bvbvbv54/ELKATEB-Hydrolic-Handbrake/prototype_commercial_v1/renders/01_FRONT_LEFT_3Q.png

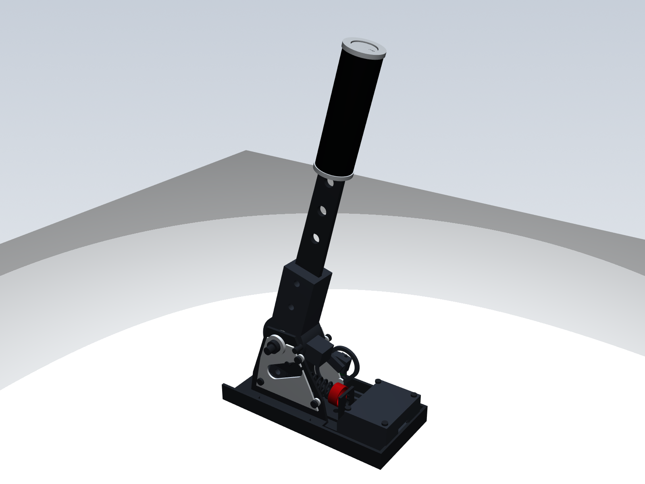
prototype_commercial_v1/renders/01_FRONT_LEFT_3Q.png
