bvbvbv54/ELKATEB-Hydrolic-Handbrake/prototype_commercial_v1/renders/02_FRONT_RIGHT_3Q.png

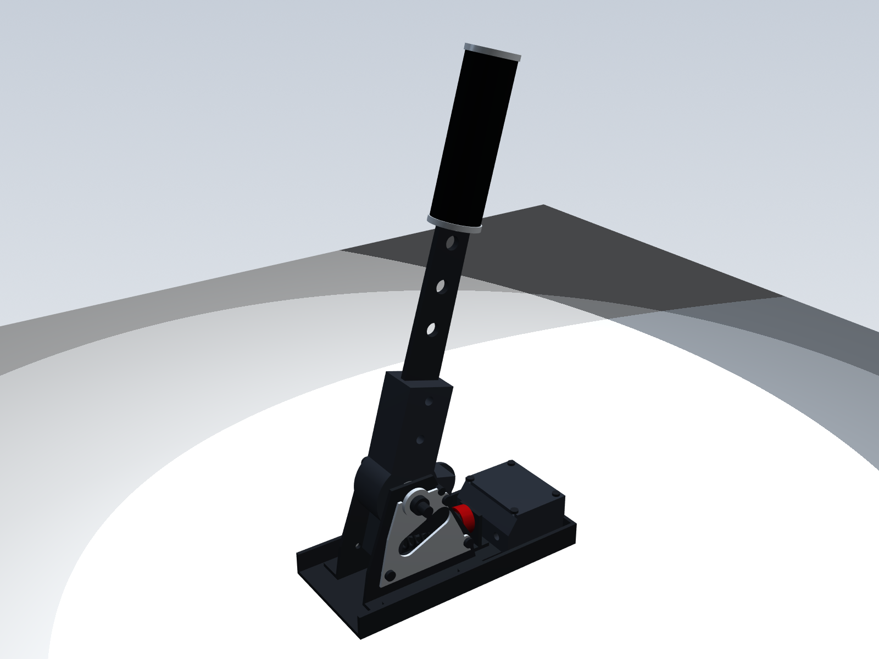
prototype_commercial_v1/renders/02_FRONT_RIGHT_3Q.png
