bvbvbv54/ELKATEB-Hydrolic-Handbrake/prototype_commercial_v1/renders/03_LEFT_SIDE.png

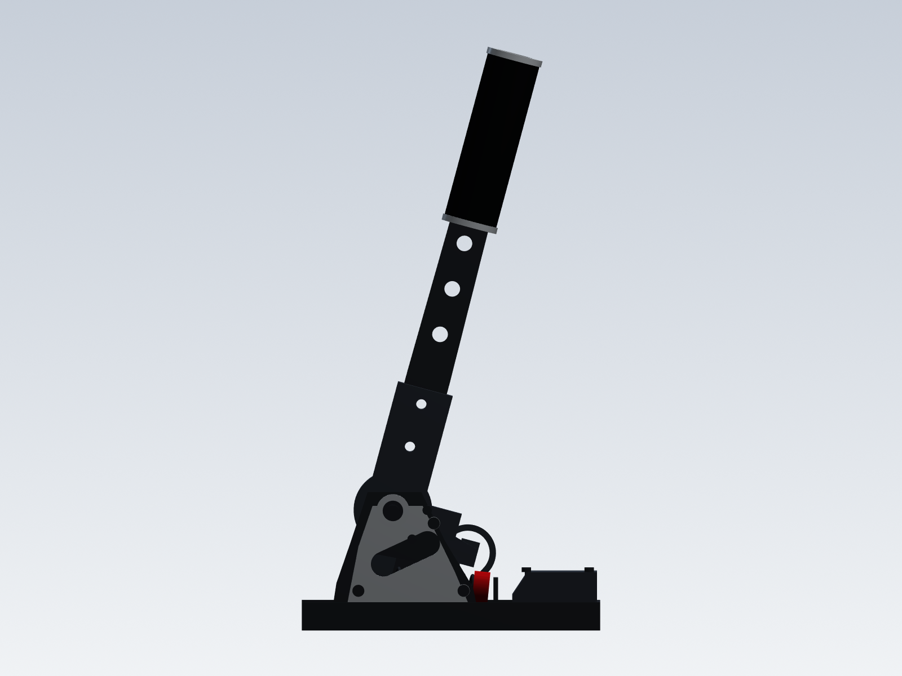
prototype_commercial_v1/renders/03_LEFT_SIDE.png
