bvbvbv54/ELKATEB-Hydrolic-Handbrake/prototype_commercial_v1/renders/07_TOP.png

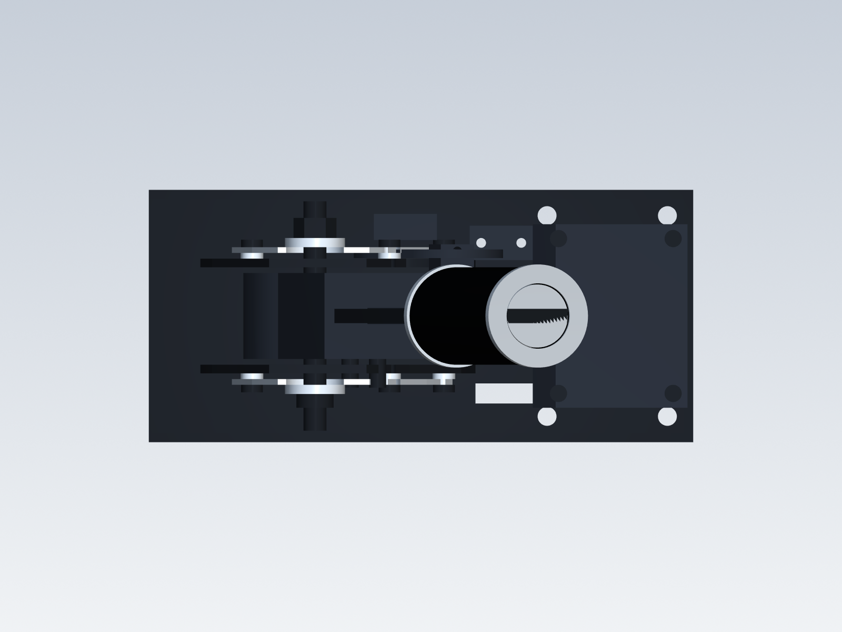
prototype_commercial_v1/renders/07_TOP.png
