bvbvbv54/ELKATEB-Hydrolic-Handbrake/prototype_commercial_v1/renders/08_LOW_ANGLE.png

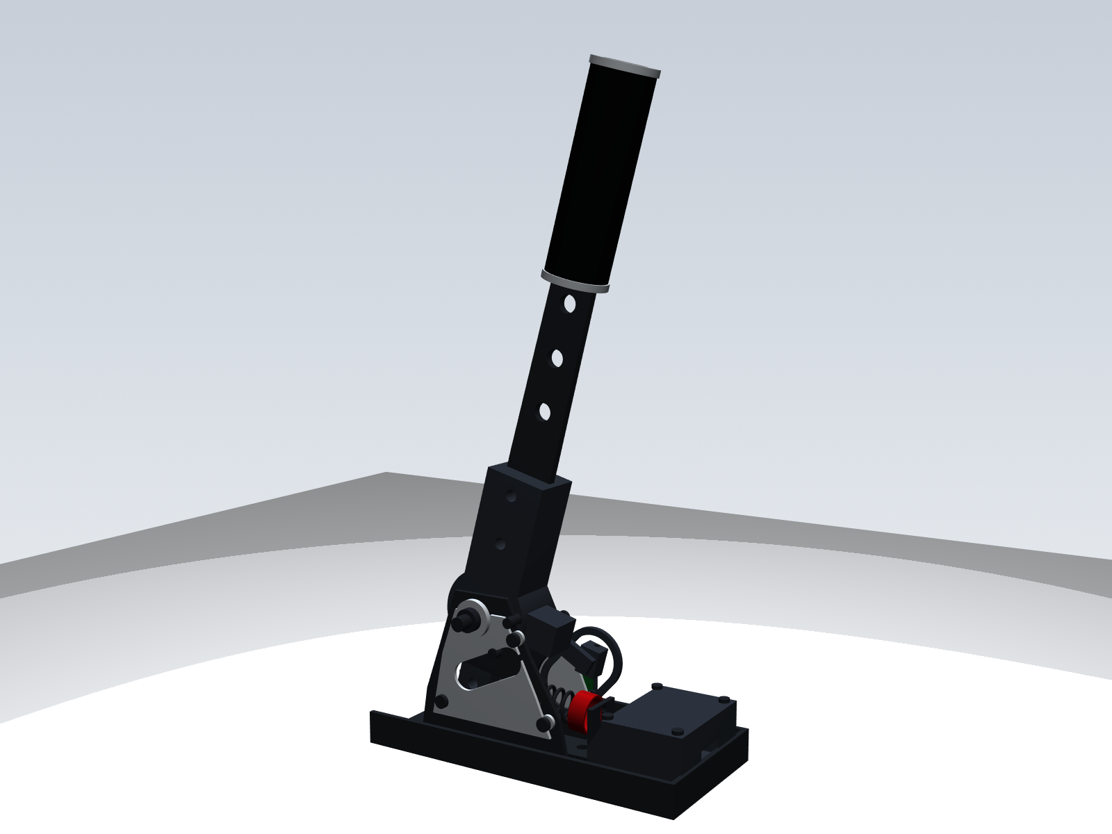
prototype_commercial_v1/renders/08_LOW_ANGLE.png
