bvbvbv54/ELKATEB-Hydrolic-Handbrake/prototype_commercial_v1/renders/11_FULL_EXPLODED_VIEW.png

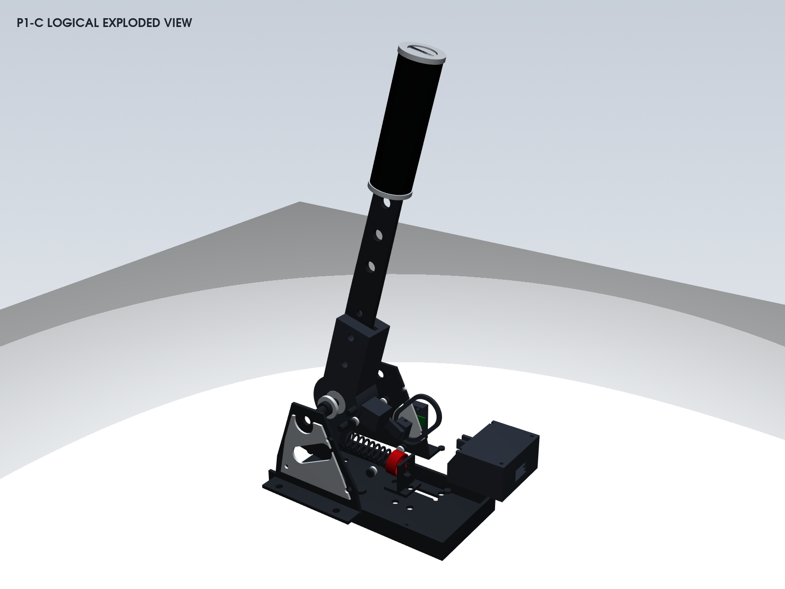
prototype_commercial_v1/renders/11_FULL_EXPLODED_VIEW.png
