bvbvbv54/ELKATEB-Hydrolic-Handbrake/prototype_commercial_v1/renders/12_INTERNAL_CUTAWAY.png

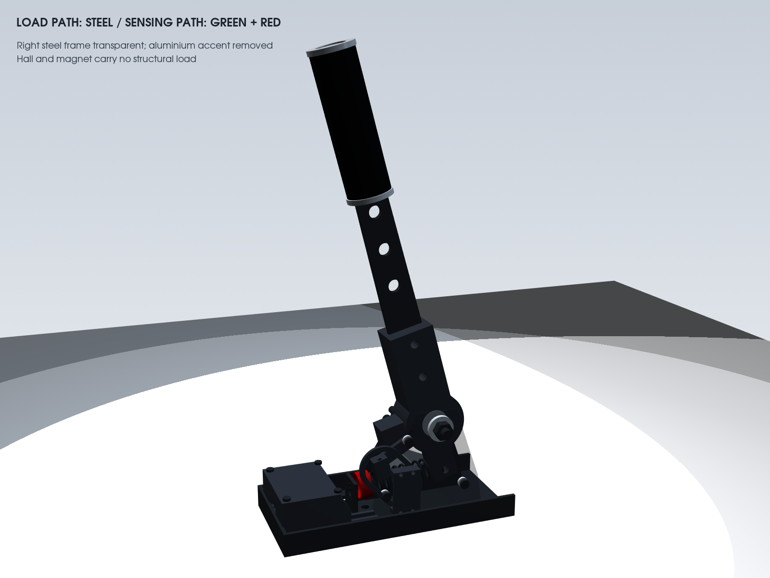
prototype_commercial_v1/renders/12_INTERNAL_CUTAWAY.png
