bvbvbv54/ELKATEB-Hydrolic-Handbrake/prototype_commercial_v1/renders/13_HALL_SENSOR_DETAIL.png

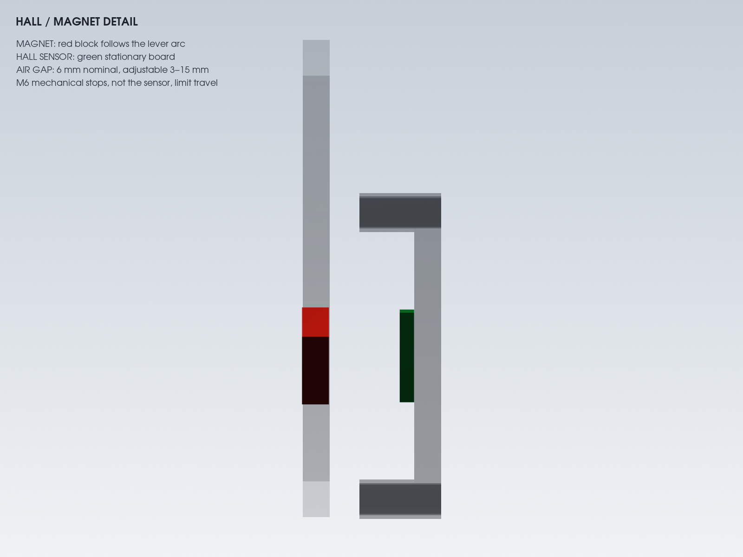
prototype_commercial_v1/renders/13_HALL_SENSOR_DETAIL.png
