bvbvbv54/ELKATEB-Hydrolic-Handbrake/prototype_commercial_v1/renders/14_SPRING_SYSTEM_DETAIL.png

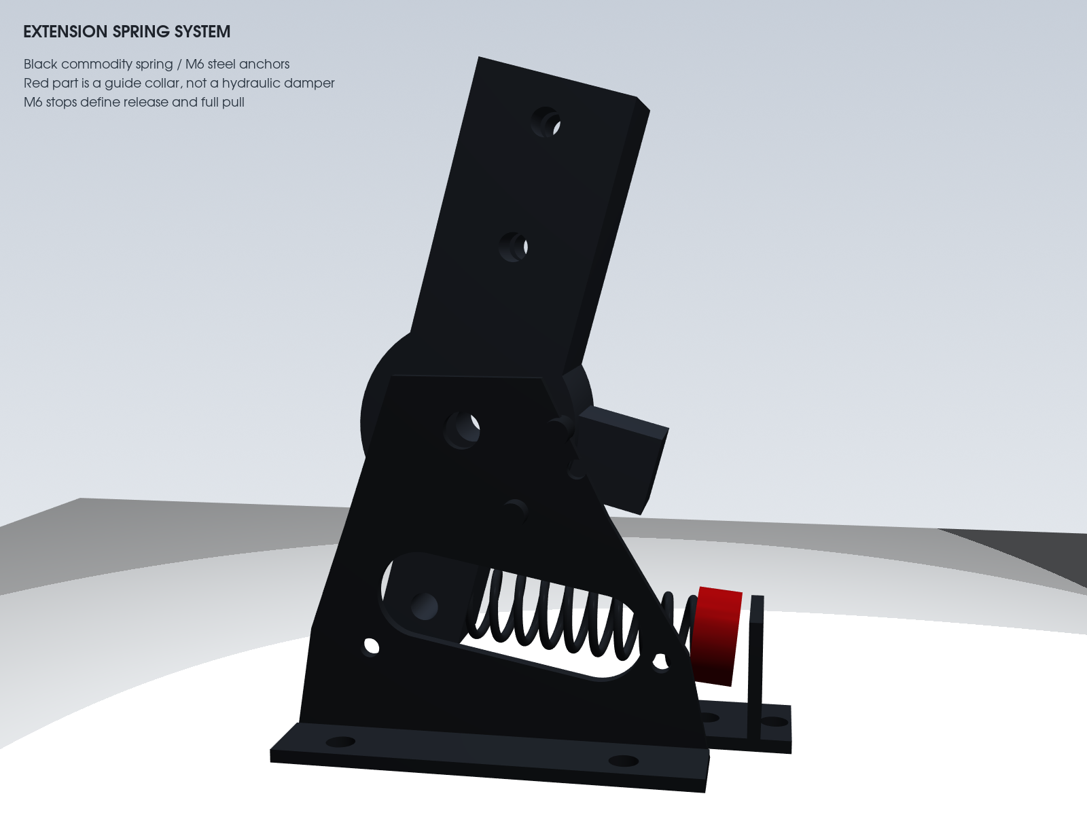
prototype_commercial_v1/renders/14_SPRING_SYSTEM_DETAIL.png
