bvbvbv54/ELKATEB-Hydrolic-Handbrake/prototype_commercial_v1/renders/15_DESK_CLAMP_REALISTIC.png

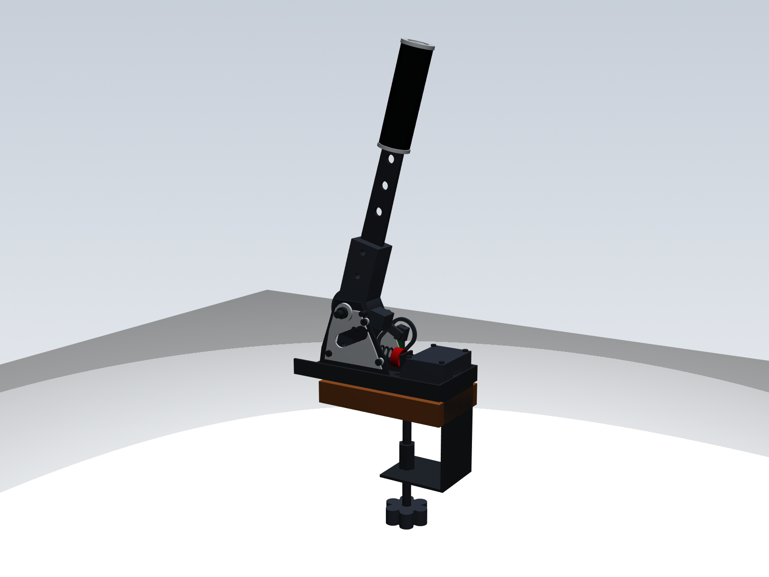
prototype_commercial_v1/renders/15_DESK_CLAMP_REALISTIC.png
