bvbvbv54/ELKATEB-Hydrolic-Handbrake/prototype_commercial_v1/renders/16_RIG_MOUNT_CONFIGURATION.png

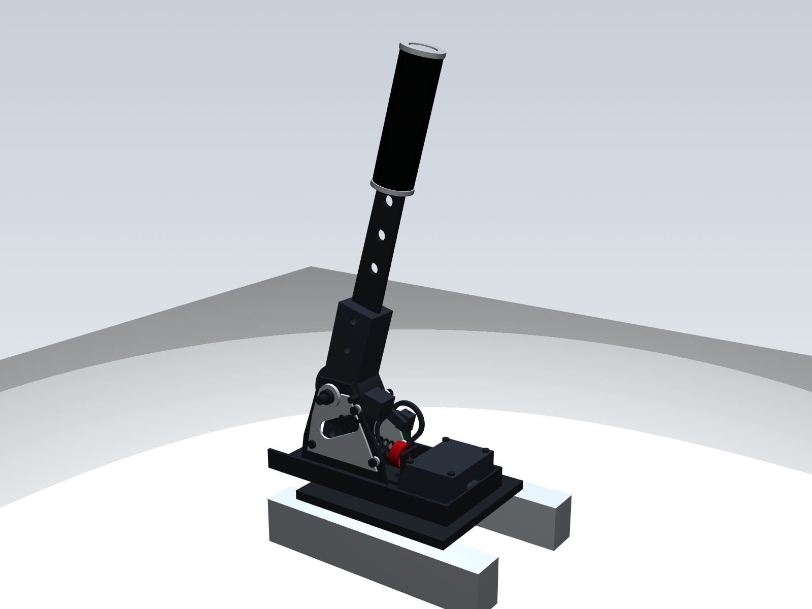
prototype_commercial_v1/renders/16_RIG_MOUNT_CONFIGURATION.png
