bvbvbv54/ELKATEB-Hydrolic-Handbrake/prototype_commercial_v1/renders/18_REAL_SIM_RIG_CONTEXT.png

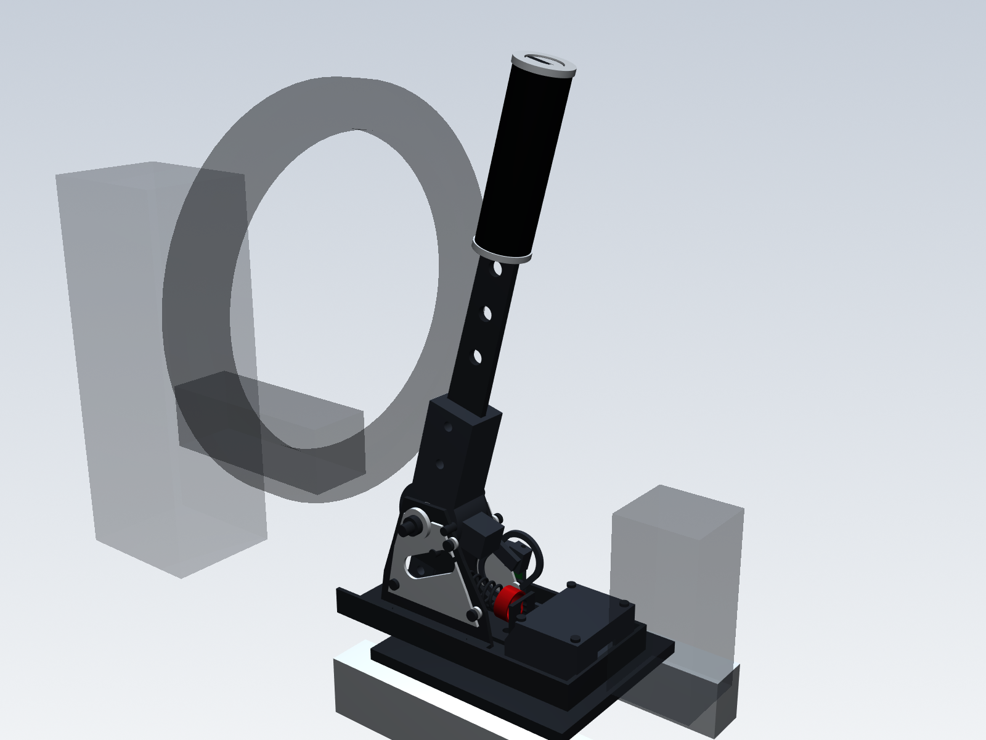
prototype_commercial_v1/renders/18_REAL_SIM_RIG_CONTEXT.png
