bvbvbv54/ELKATEB-Hydrolic-Handbrake/prototype_p1/renders/02_LEFT_SIDE.png

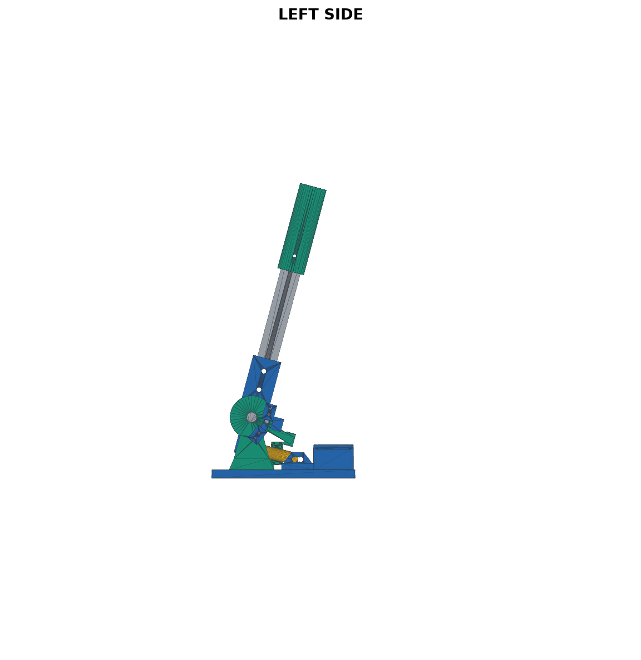
prototype_p1/renders/02_LEFT_SIDE.png
