bvbvbv54/ELKATEB-Hydrolic-Handbrake/prototype_p1/renders/04_FRONT.png

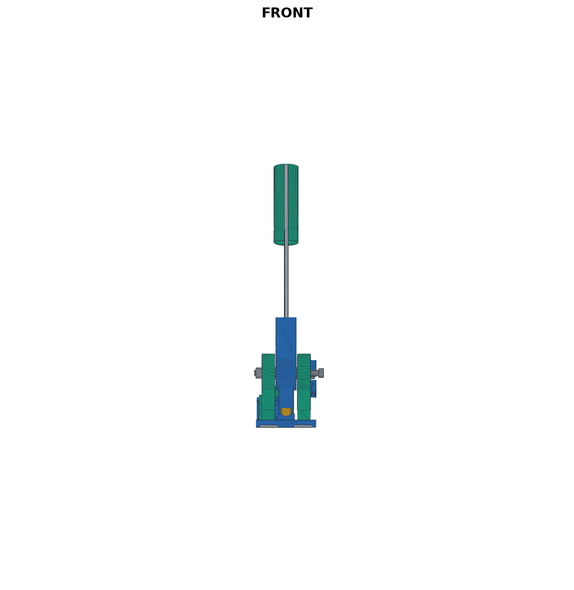
prototype_p1/renders/04_FRONT.png
