bvbvbv54/ELKATEB-Hydrolic-Handbrake/prototype_p1/renders/06_TOP.png

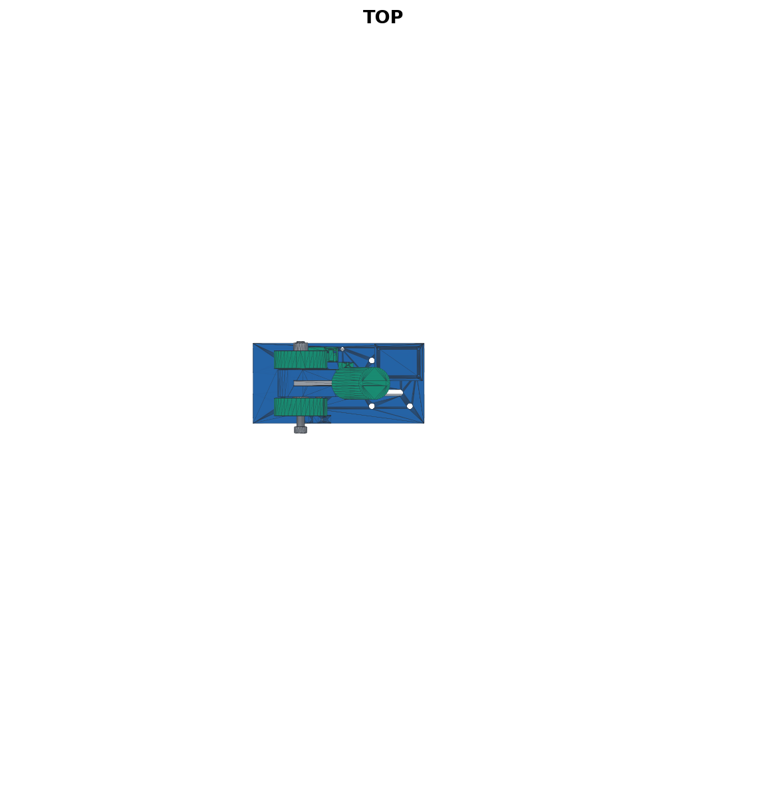
prototype_p1/renders/06_TOP.png
