bvbvbv54/ELKATEB-Hydrolic-Handbrake/prototype_p1/renders/07_BOTTOM.png

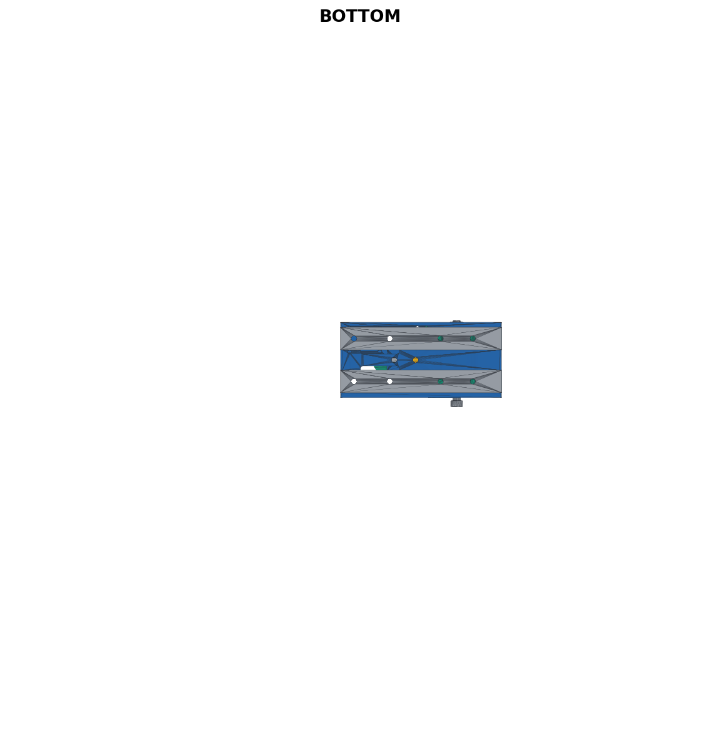
prototype_p1/renders/07_BOTTOM.png
