bvbvbv54/ELKATEB-Hydrolic-Handbrake/prototype_p1/renders/08_PIVOT_SECTION.png

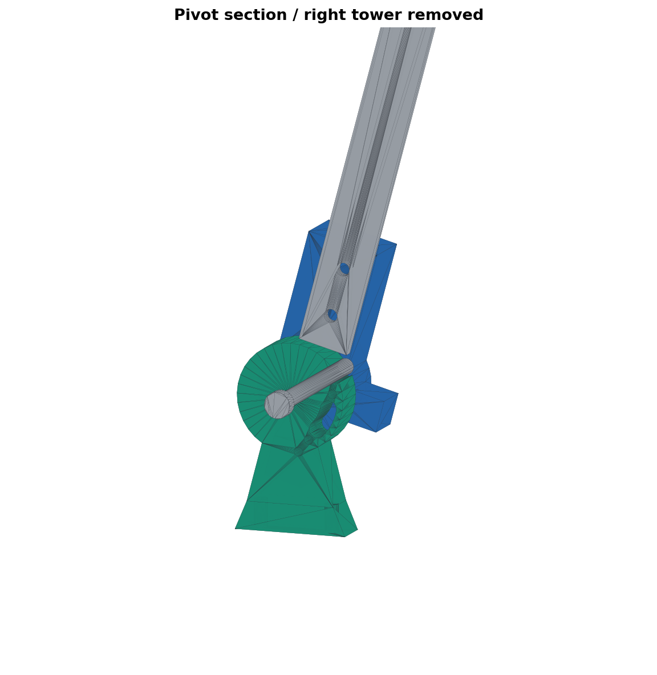
prototype_p1/renders/08_PIVOT_SECTION.png
