bvbvbv54/ELKATEB-Hydrolic-Handbrake/prototype_p1/renders/14_MID_TRAVEL.png

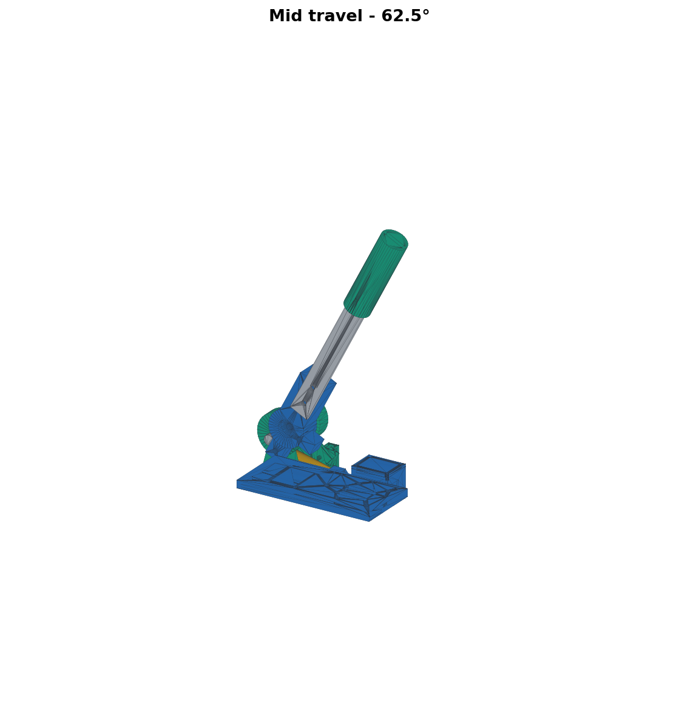
prototype_p1/renders/14_MID_TRAVEL.png
