bvbvbv54/ELKATEB-Hydrolic-Handbrake/prototype_p1/renders/16_CLAMP_10MM_DESK.png

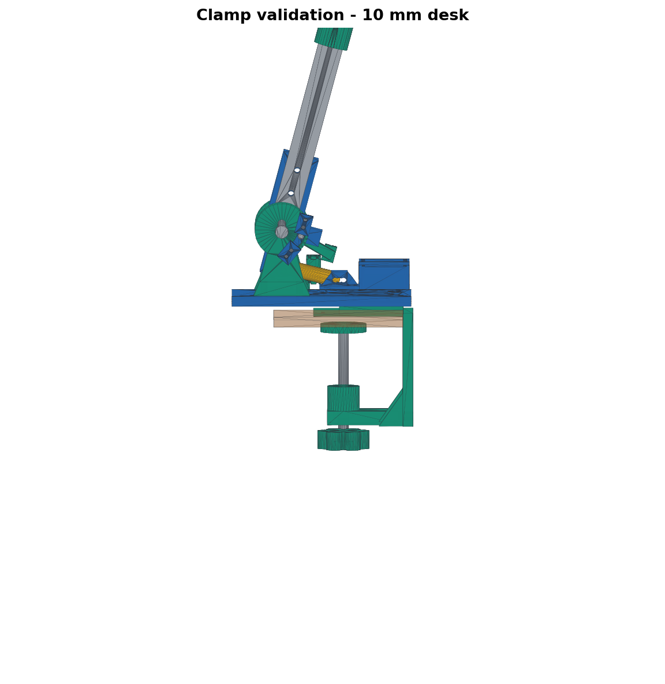
prototype_p1/renders/16_CLAMP_10MM_DESK.png
