bvbvbv54/ELKATEB-Hydrolic-Handbrake/prototype_commercial_v1/step/P1C-P002_MAGNET_CARRIER.step

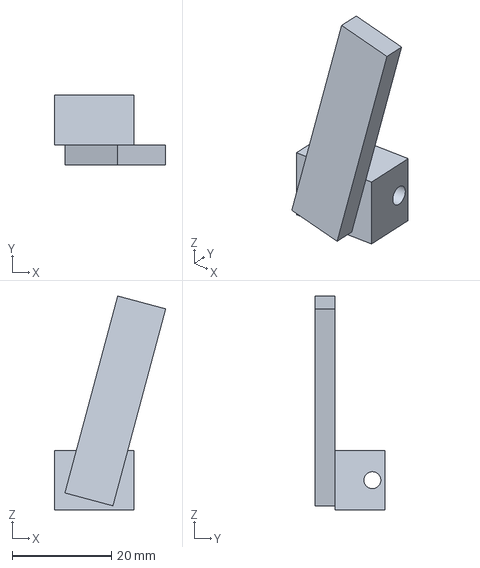
[picture p38: CAD file, 2026-09-27]
prototype_commercial_v1/step/P1C-P002_MAGNET_CARRIER.step
22.4 x 14.0 x 43.0 mm
