bvbvbv54/ELKATEB-Hydrolic-Handbrake/prototype_p1/printer_handoff_amine/01_CALIBRATION_FIRST/COUPON_HALL_GAP_JIG.stl

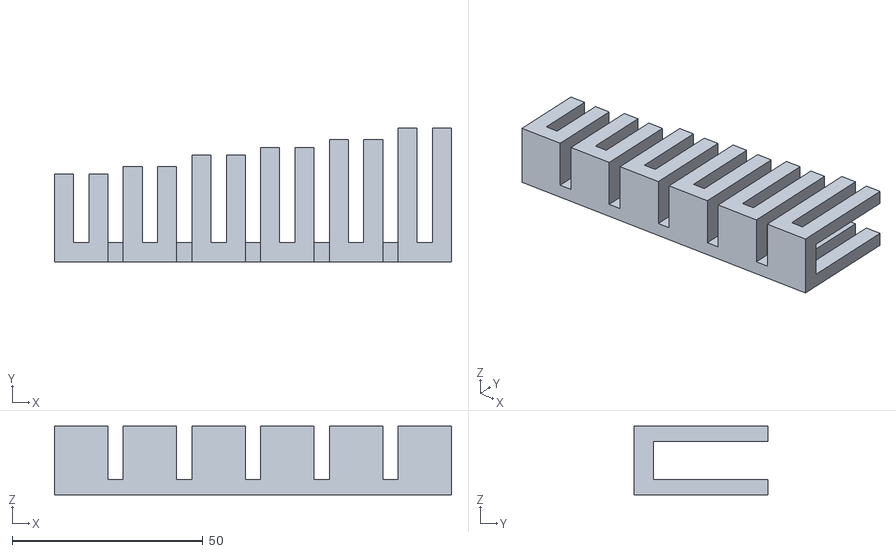
[picture p39: CAD file, 2026-09-27]
prototype_p1/printer_handoff_amine/01_CALIBRATION_FIRST/COUPON_HALL_GAP_JIG.stl
104.0 x 35.0 x 18.0
