bvbvbv54/ELKATEB-Hydrolic-Handbrake/prototype_p1/printer_handoff_amine/02_MECHANICAL_CORE_AFTER_CALIBRATION/P1-003_RIGHT_PIVOT_SUPPORT.stl

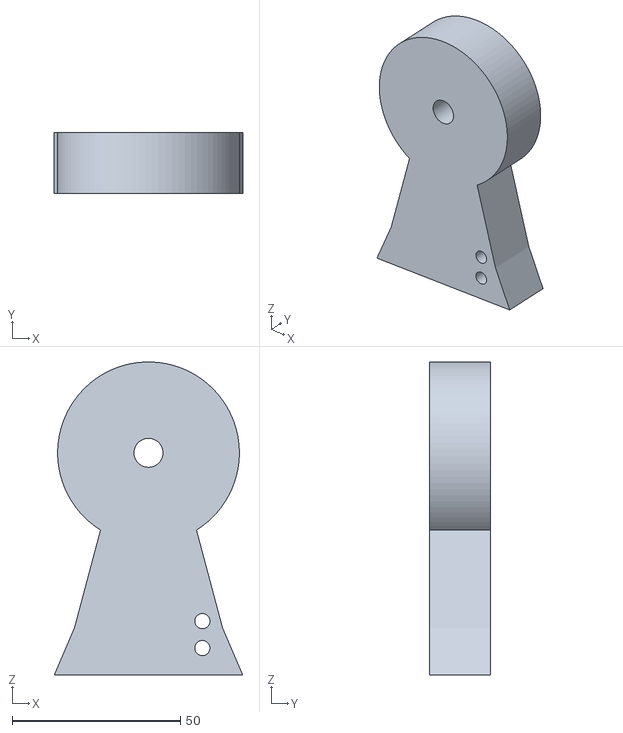
[picture p40: CAD file, 2026-09-27]
prototype_p1/printer_handoff_amine/02_MECHANICAL_CORE_AFTER_CALIBRATION/P1-003_RIGHT_PIVOT_SUPPORT.stl
56.0 x 18.0 x 93.0
