bvbvbv54/ELKATEB-Hydrolic-Handbrake/prototype_p1/printer_handoff_amine/03_SENSOR_AND_ELECTRONICS/P1-011A_HALL_FIXED_BRACKET.stl

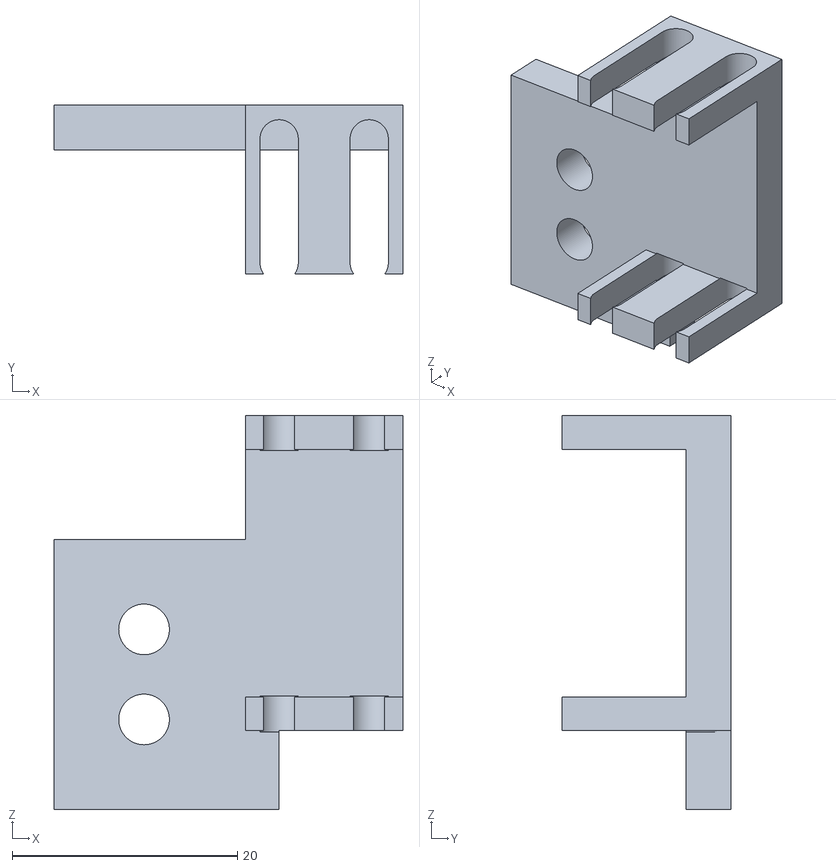
[picture p41: CAD file, 2026-09-27]
prototype_p1/printer_handoff_amine/03_SENSOR_AND_ELECTRONICS/P1-011A_HALL_FIXED_BRACKET.stl
31.0 x 15.0 x 35.0
