bvbvbv54/ELKATEB-Hydrolic-Handbrake/prototype_p1/printer_handoff_amine/04_TABLE_CLAMP/P1-024_SWIVEL_PAD_HOLDER.stl

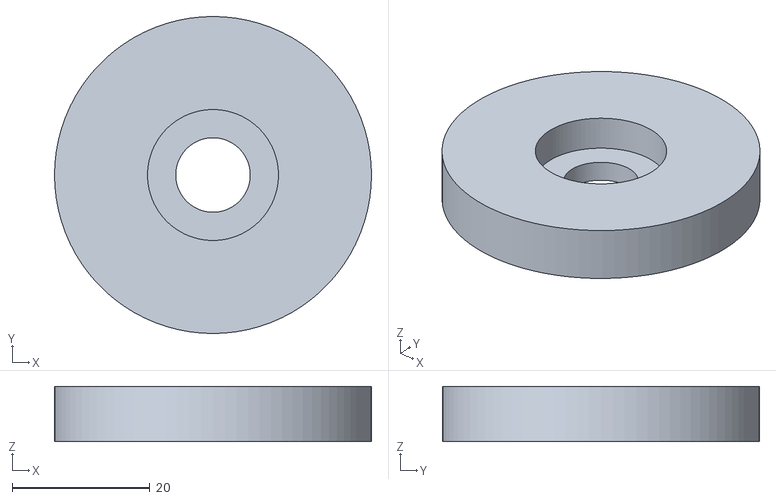
[picture p42: CAD file, 2026-09-27]
prototype_p1/printer_handoff_amine/04_TABLE_CLAMP/P1-024_SWIVEL_PAD_HOLDER.stl
46.0 x 46.0 x 8.00
