bvbvbv54/ELKATEB-Hydrolic-Handbrake/prototype_p1/step/P1-002_LEFT_PIVOT_SUPPORT.step

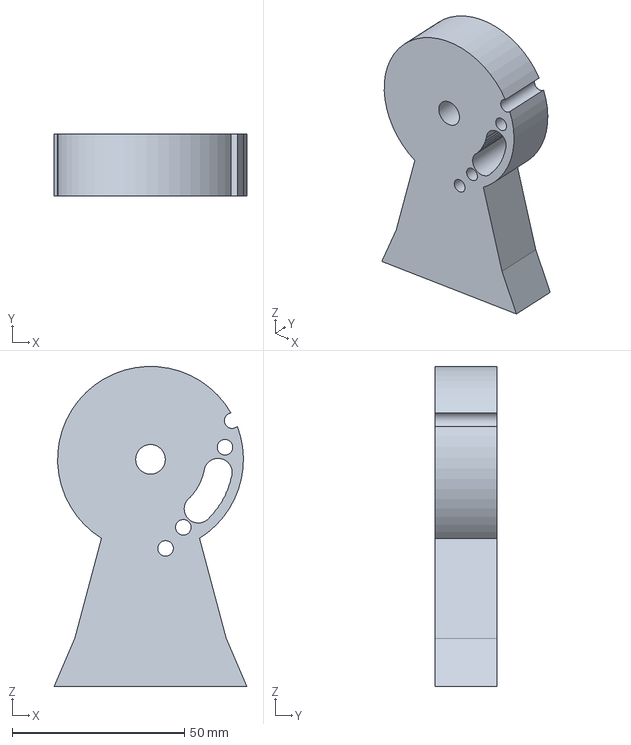
[picture p43: CAD file, 2026-09-27]
prototype_p1/step/P1-002_LEFT_PIVOT_SUPPORT.step
56.0 x 18.0 x 93.0 mm
