bvbvbv54/ELKATEB-Hydrolic-Handbrake/prototype_commercial_v1/dxf/P1C-S003_RIGHT_SIDE_FRAME_FLAT.dxf

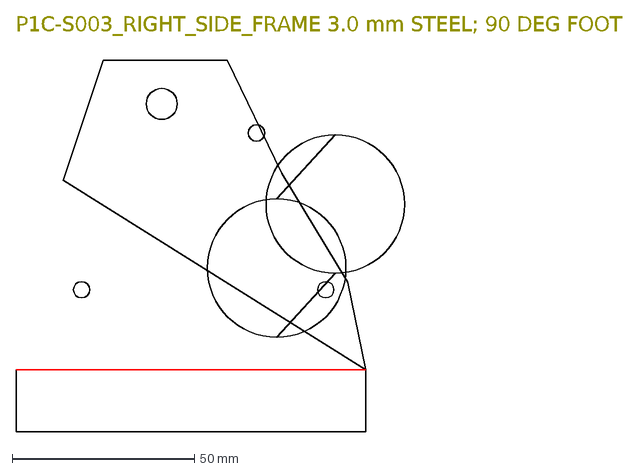
[picture p44: CAD file, 2026-09-27]
prototype_commercial_v1/dxf/P1C-S003_RIGHT_SIDE_FRAME_FLAT.dxf
P1C-S003_RIGHT_SIDE_FRAME 3.0 mm STEEL; 90 DEG FOOT
