bvbvbv54/ELKATEB-Hydrolic-Handbrake/prototype_commercial_v1/step/P1C-P001_BEARING_HUB.step

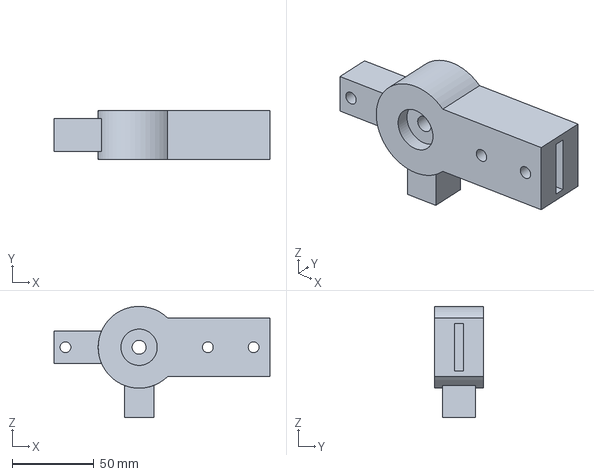
[picture p45: CAD file, 2026-09-27]
prototype_commercial_v1/step/P1C-P001_BEARING_HUB.step
132.0 x 30.0 x 68.0 mm
