bvbvbv54/ELKATEB-Hydrolic-Handbrake/prototype_p1/coupons/COUPON_M6_CLEARANCE.step

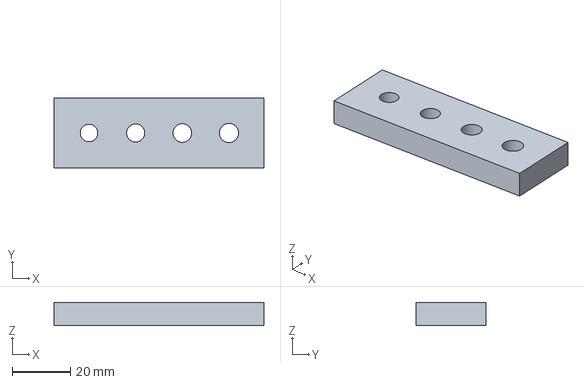
[picture p46: CAD file, 2026-09-27]
prototype_p1/coupons/COUPON_M6_CLEARANCE.step
72.0 x 24.0 x 8.00 mm
