bvbvbv54/ELKATEB-Hydrolic-Handbrake/prototype_p1/printer_handoff_amine/02_MECHANICAL_CORE_AFTER_CALIBRATION/P1-001_BASE.stl

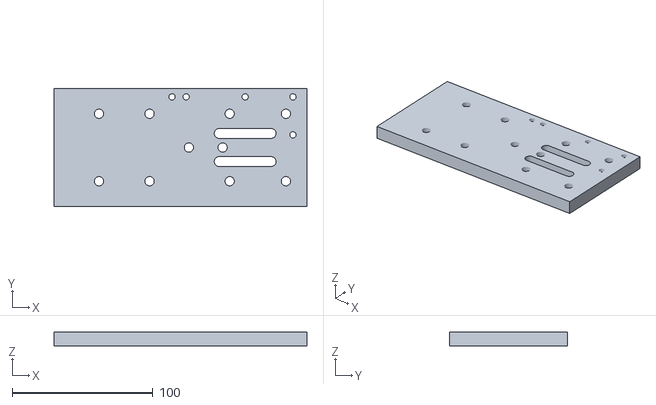
[picture p47: CAD file, 2026-09-27]
prototype_p1/printer_handoff_amine/02_MECHANICAL_CORE_AFTER_CALIBRATION/P1-001_BASE.stl
180.0 x 84.0 x 10.0
