bvbvbv54/ELKATEB-Hydrolic-Handbrake/prototype_p1/printer_handoff_amine/03_SENSOR_AND_ELECTRONICS/P1-013_ELECTRONICS_COVER.stl

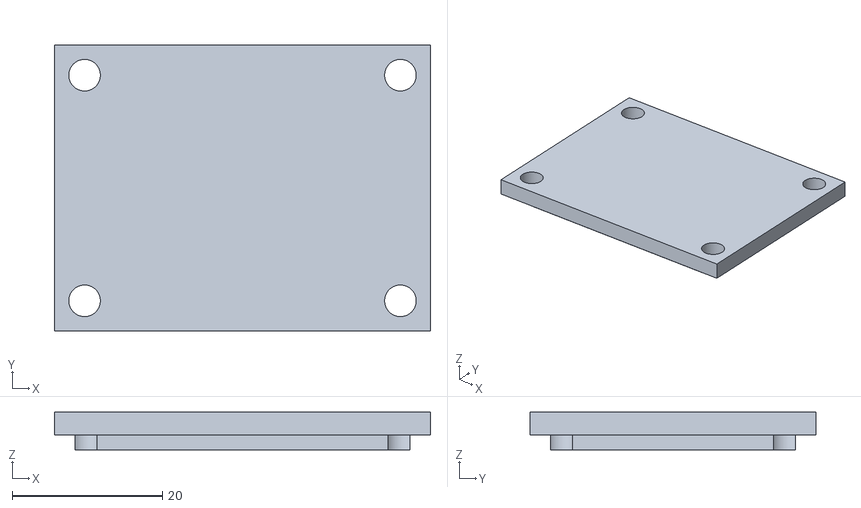
[picture p48: CAD file, 2026-09-27]
prototype_p1/printer_handoff_amine/03_SENSOR_AND_ELECTRONICS/P1-013_ELECTRONICS_COVER.stl
50.0 x 38.0 x 5.00
