bvbvbv54/ELKATEB-Hydrolic-Handbrake/prototype_p1/printer_handoff_amine/04_TABLE_CLAMP/P1-020_CLAMP_BASE_INTERFACE.stl

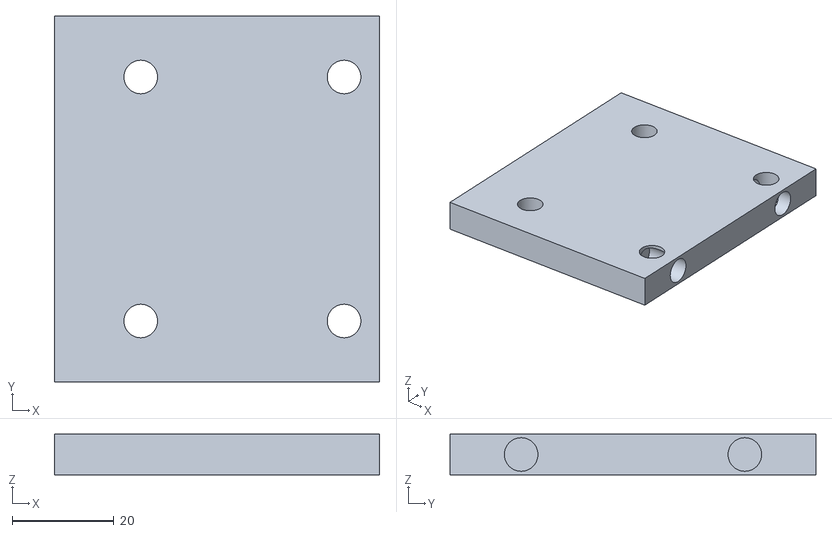
[picture p49: CAD file, 2026-09-27]
prototype_p1/printer_handoff_amine/04_TABLE_CLAMP/P1-020_CLAMP_BASE_INTERFACE.stl
64.0 x 72.0 x 8.00
