bvbvbv54/ELKATEB-Hydrolic-Handbrake/prototype_commercial_v1/dxf/P1C-S006_CLAMP_BRACKET_FLAT.dxf

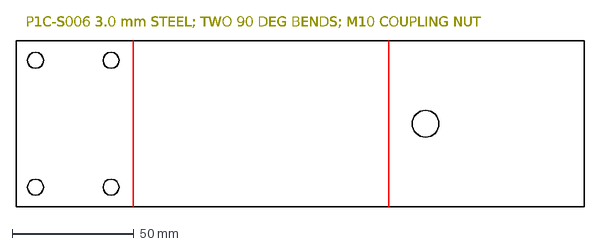
[picture p50: CAD file, 2026-09-27]
prototype_commercial_v1/dxf/P1C-S006_CLAMP_BRACKET_FLAT.dxf
P1C-S006 3.0 mm STEEL; TWO 90 DEG BENDS; M10 COUPLING NUT
