bvbvbv54/ELKATEB-Hydrolic-Handbrake/prototype_commercial_v1/manufacturing_rfq/STEEL/P1C-S002_LEFT_SIDE_FRAME_FLAT.dxf

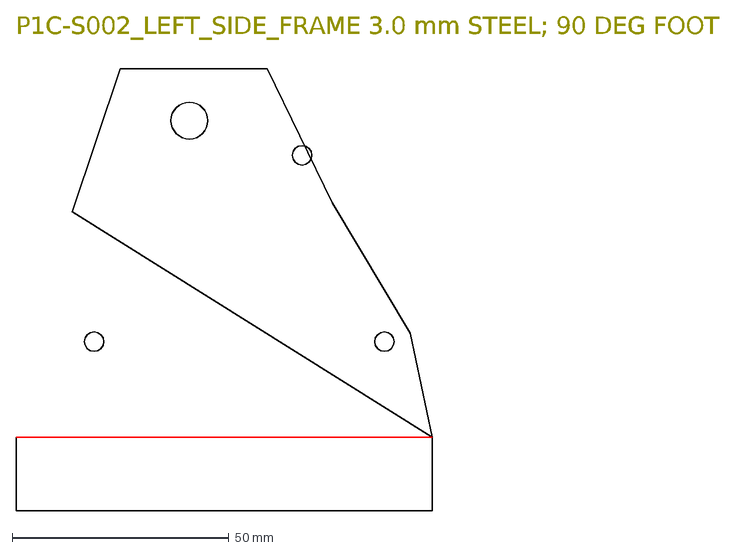
[picture p51: CAD file, 2026-09-27]
prototype_commercial_v1/manufacturing_rfq/STEEL/P1C-S002_LEFT_SIDE_FRAME_FLAT.dxf
P1C-S002_LEFT_SIDE_FRAME 3.0 mm STEEL; 90 DEG FOOT
