bvbvbv54/ELKATEB-Hydrolic-Handbrake/prototype_commercial_v1/step/P1C-A001_LEFT_ACCENT.step

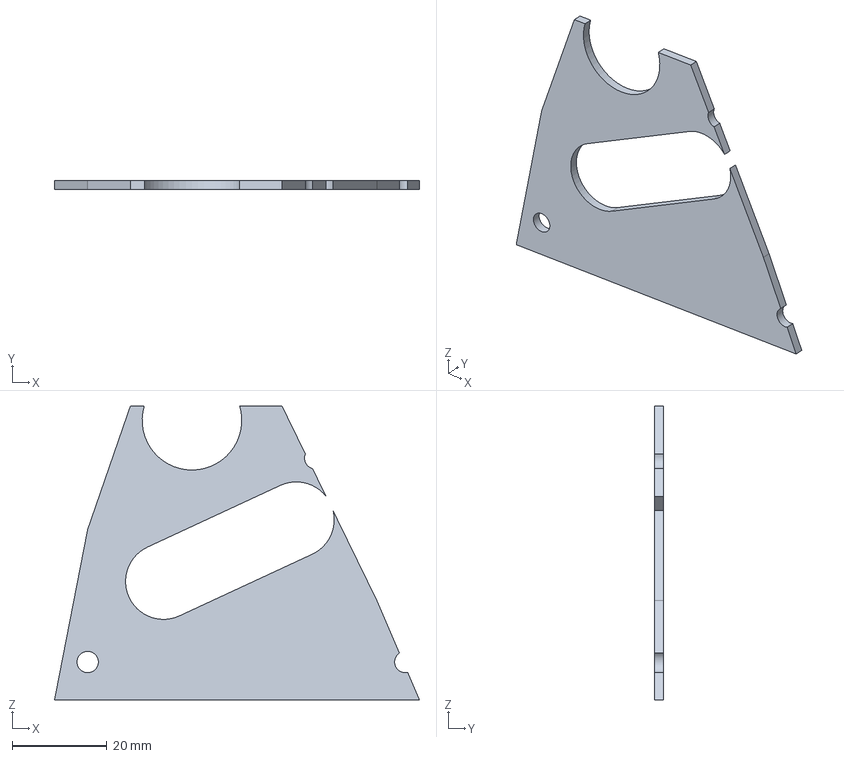
[picture p52: CAD file, 2026-09-27]
prototype_commercial_v1/step/P1C-A001_LEFT_ACCENT.step
77.0 x 2.00 x 62.0 mm
