bvbvbv54/ELKATEB-Hydrolic-Handbrake/prototype_p1/coupons/COUPON_608_POCKETS_DEPTH_7.step

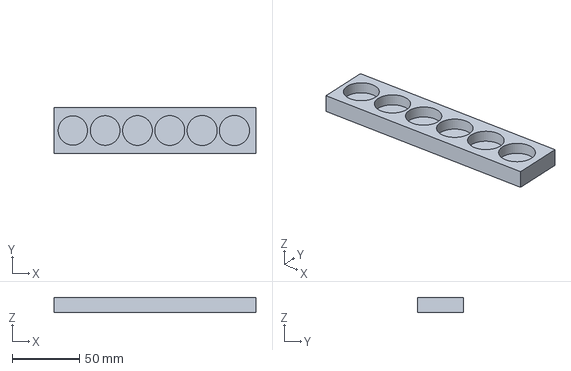
[picture p53: CAD file, 2026-09-27]
prototype_p1/coupons/COUPON_608_POCKETS_DEPTH_7.step
150.0 x 34.0 x 11.0 mm
