bvbvbv54/ELKATEB-Hydrolic-Handbrake/prototype_p1/printer_handoff_amine/02_MECHANICAL_CORE_AFTER_CALIBRATION/P1-007_SPRING_ANCHOR_MODULE.stl

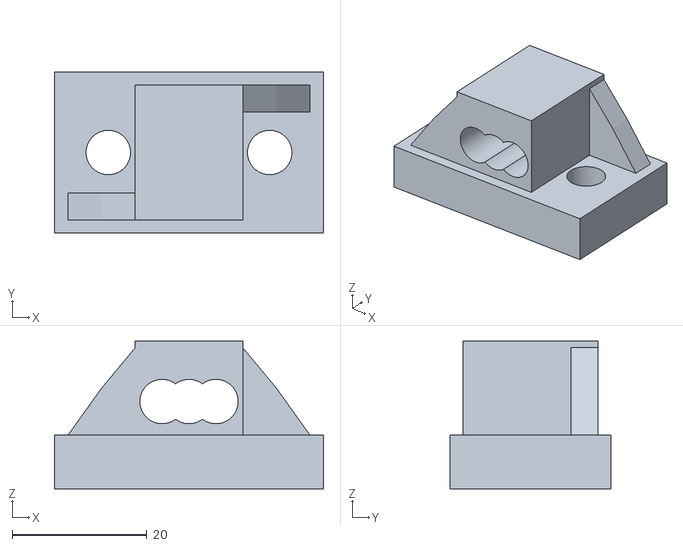
[picture p54: CAD file, 2026-09-27]
prototype_p1/printer_handoff_amine/02_MECHANICAL_CORE_AFTER_CALIBRATION/P1-007_SPRING_ANCHOR_MODULE.stl
40.0 x 24.0 x 22.0
