bvbvbv54/ELKATEB-Hydrolic-Handbrake/prototype_p1/printer_handoff_amine/03_SENSOR_AND_ELECTRONICS/P1-010_MAGNET_HOLDER.stl

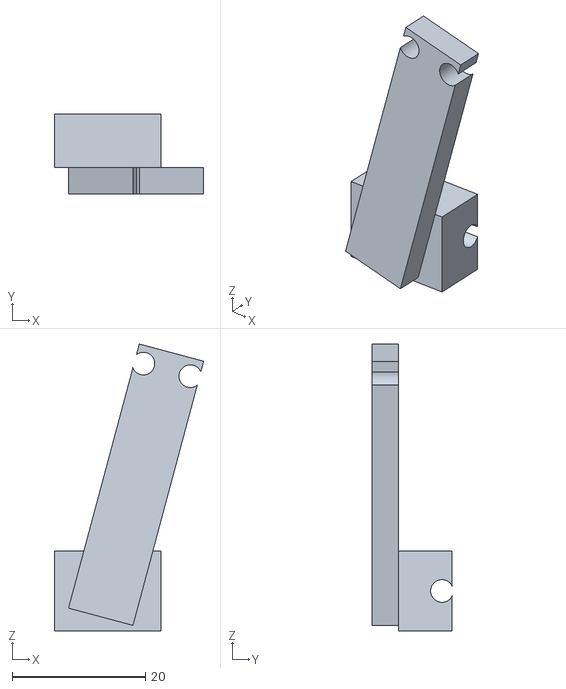
[picture p55: CAD file, 2026-09-27]
prototype_p1/printer_handoff_amine/03_SENSOR_AND_ELECTRONICS/P1-010_MAGNET_HOLDER.stl
22.4 x 12.0 x 43.0
