bvbvbv54/ELKATEB-Hydrolic-Handbrake/prototype_p1/printer_handoff_amine/04_TABLE_CLAMP/P1-025_UPPER_RUBBER_PAD_HOLDER.stl

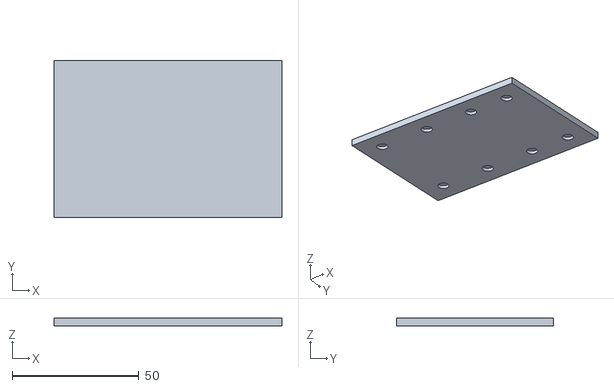
[picture p56: CAD file, 2026-09-27]
prototype_p1/printer_handoff_amine/04_TABLE_CLAMP/P1-025_UPPER_RUBBER_PAD_HOLDER.stl
90.0 x 62.0 x 3.00
