bvbvbv54/ELKATEB-Hydrolic-Handbrake/prototype_p1/coupons/COUPON_LOADED_BEARING_WALL.step

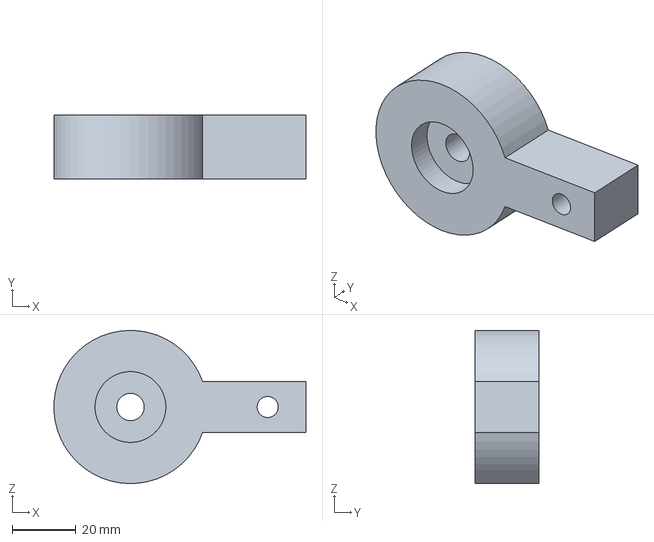
[picture p58: CAD file, 2026-09-27]
prototype_p1/coupons/COUPON_LOADED_BEARING_WALL.step
79.0 x 20.0 x 48.0 mm
