bvbvbv54/ELKATEB-Hydrolic-Handbrake/prototype_p1/printer_handoff_amine/02_MECHANICAL_CORE_AFTER_CALIBRATION/P1-008_RELEASE_STOP.stl

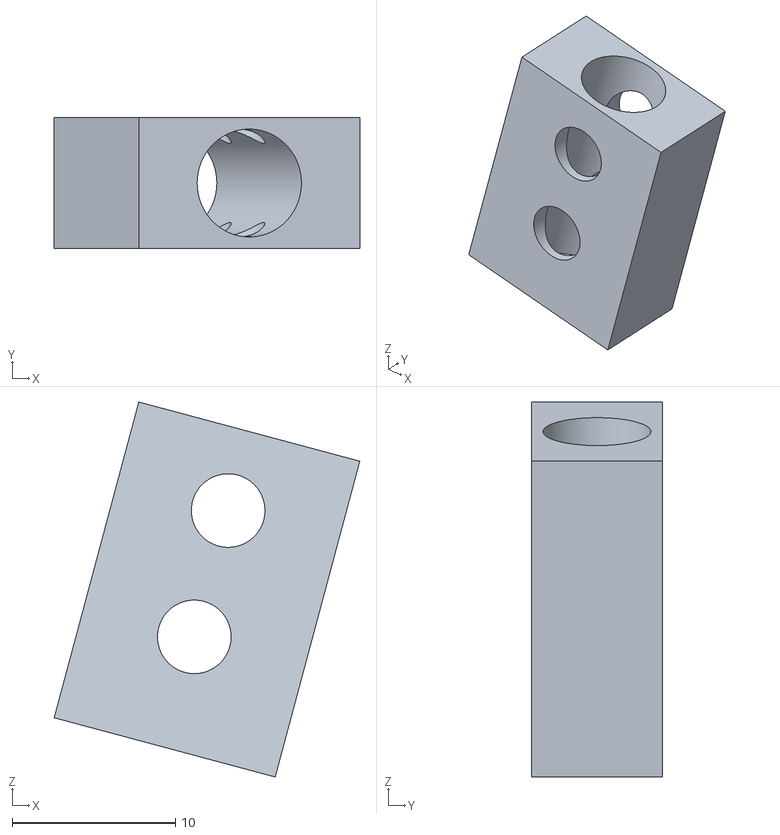
[picture p59: CAD file, 2026-09-27]
prototype_p1/printer_handoff_amine/02_MECHANICAL_CORE_AFTER_CALIBRATION/P1-008_RELEASE_STOP.stl
18.7 x 8.00 x 22.9
