bvbvbv54/ELKATEB-Hydrolic-Handbrake/prototype_p1/printer_handoff_amine/03_SENSOR_AND_ELECTRONICS/P1-012_ELECTRONICS_ENCLOSURE.stl

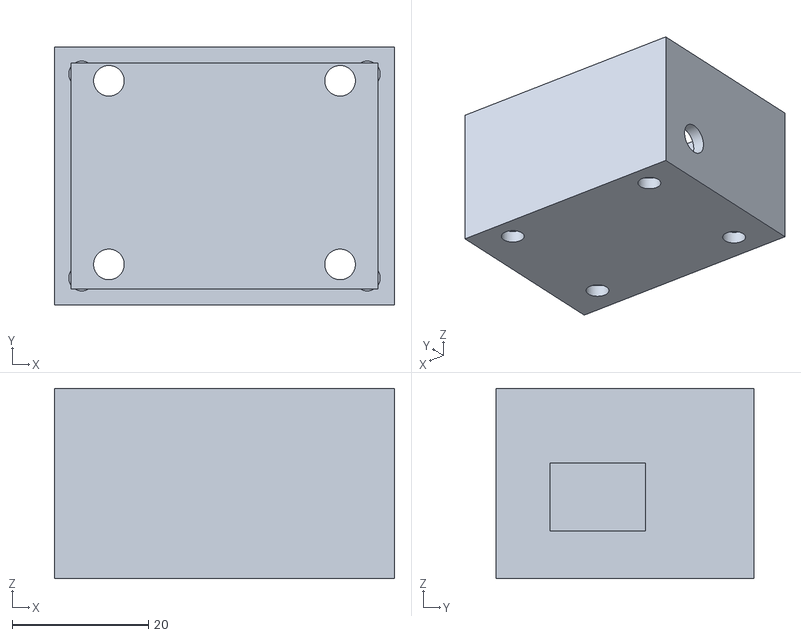
[picture p60: CAD file, 2026-09-27]
prototype_p1/printer_handoff_amine/03_SENSOR_AND_ELECTRONICS/P1-012_ELECTRONICS_ENCLOSURE.stl
50.0 x 38.0 x 28.0
