bvbvbv54/ELKATEB-Hydrolic-Handbrake/prototype_p1/printer_handoff_amine/04_TABLE_CLAMP/P1-023_CLAMP_KNOB.stl

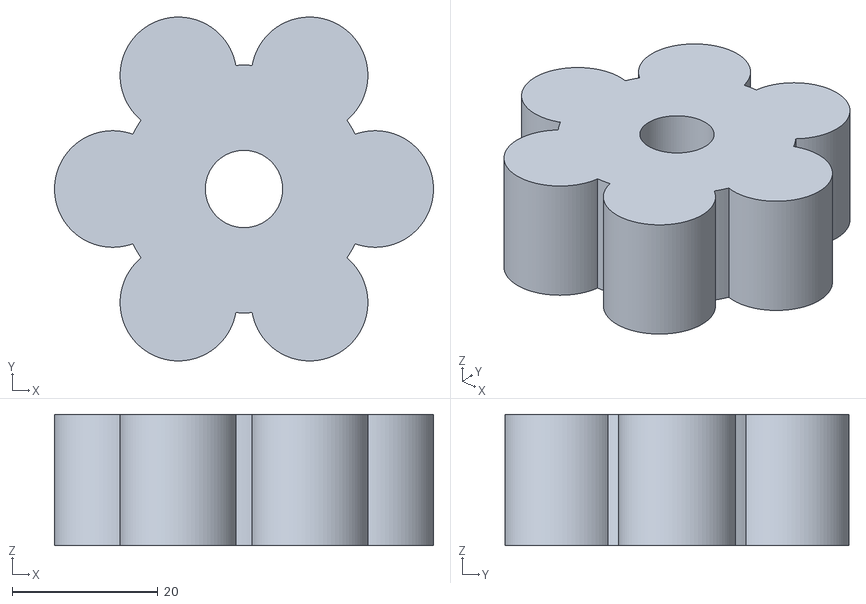
[picture p61: CAD file, 2026-09-27]
prototype_p1/printer_handoff_amine/04_TABLE_CLAMP/P1-023_CLAMP_KNOB.stl
52.0 x 47.2 x 18.0
