bvbvbv54/ELKATEB-Hydrolic-Handbrake/prototype_commercial_v1/step/P1C-S006_CLAMP_BRACKET.step

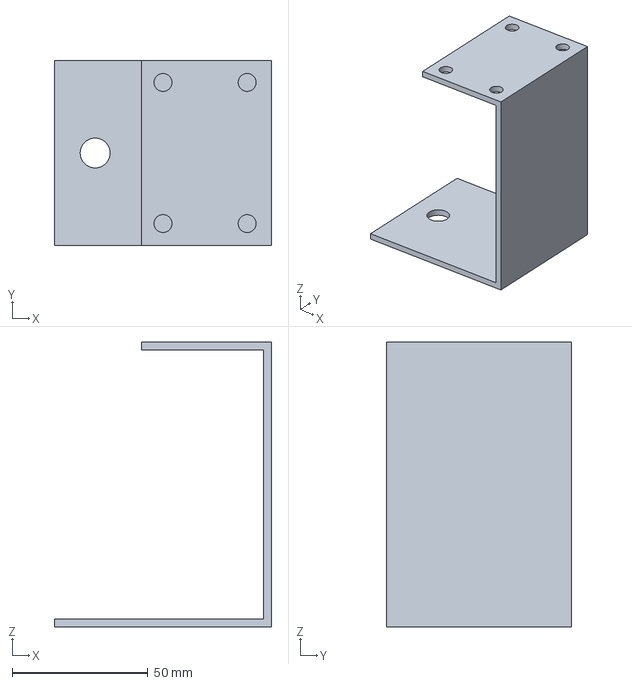
[picture p62: CAD file, 2026-09-27]
prototype_commercial_v1/step/P1C-S006_CLAMP_BRACKET.step
80.0 x 68.0 x 105.0 mm
