bvbvbv54/ELKATEB-Hydrolic-Handbrake/prototype_p1/printer_handoff_amine/01_CALIBRATION_FIRST/COUPON_MAGNET_POCKETS.stl

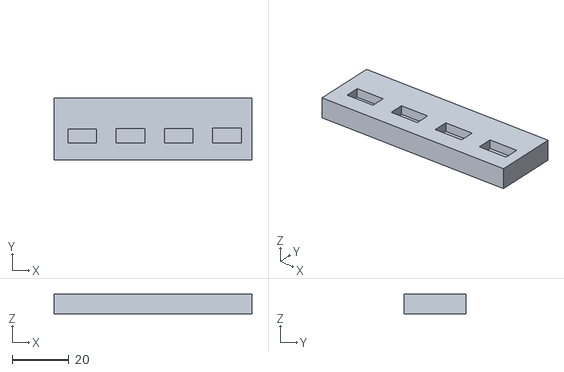
[picture p63: CAD file, 2026-09-27]
prototype_p1/printer_handoff_amine/01_CALIBRATION_FIRST/COUPON_MAGNET_POCKETS.stl
70.0 x 22.0 x 7.00
