bvbvbv54/ELKATEB-Hydrolic-Handbrake/prototype_p1/step/P1-004_LEVER_ROOT_BEARING_HUB.step

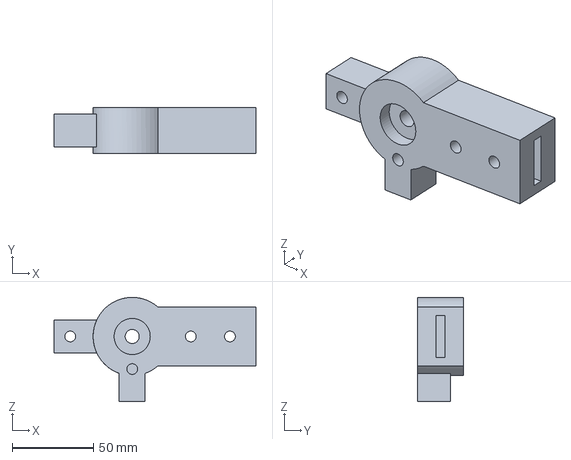
[picture p64: CAD file, 2026-09-27]
prototype_p1/step/P1-004_LEVER_ROOT_BEARING_HUB.step
124.0 x 28.0 x 64.0 mm
