bvbvbv54/ELKATEB-Hydrolic-Handbrake/prototype_p1/step/P1-005_STEEL_LEVER_TEMPLATE.step

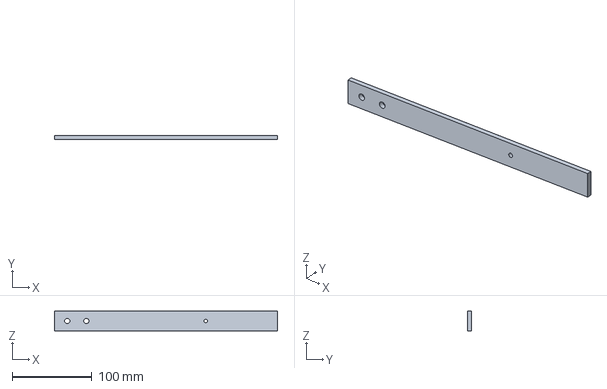
[picture p66: CAD file, 2026-09-27]
prototype_p1/step/P1-005_STEEL_LEVER_TEMPLATE.step
280.0 x 5.00 x 25.0 mm
