bvbvbv54/ELKATEB-Hydrolic-Handbrake/prototype_commercial_v1/step/P1C-P005_ELECTRONICS_POD.step

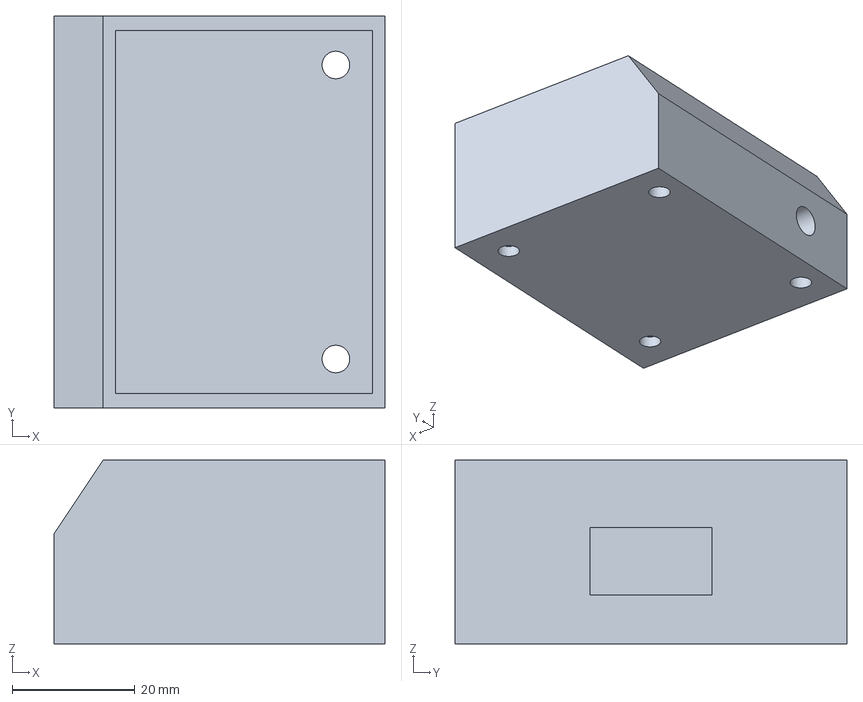
[picture p68: CAD file, 2026-09-27]
prototype_commercial_v1/step/P1C-P005_ELECTRONICS_POD.step
54.0 x 64.0 x 30.0 mm
