bvbvbv54/ELKATEB-Hydrolic-Handbrake/prototype_p1/step/P1_CLAMP_10MM_DESK.step

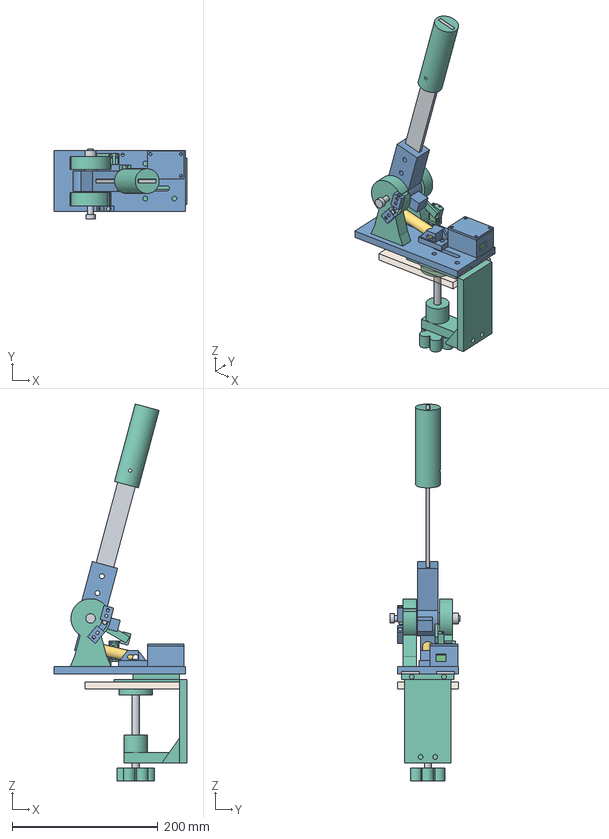
[picture p69: CAD file, 2026-09-27]
prototype_p1/step/P1_CLAMP_10MM_DESK.step
182.0 x 96.0 x 517.2 mm
P1-001_BASE
P1-030_LEFT_BACKING_STRIP
P1-031_RIGHT_BACKING_STRIP
P1-002_LEFT_PIVOT_SUPPORT
P1-003_RIGHT_PIVOT_SUPPORT
P1-007_SPRING_ANCHOR_MODULE
P1-008_RELEASE_STOP
P1-009_FULL_PULL_STOP
P1-012_ELECTRONICS_ENCLOSURE
P1-013_ELECTRONICS_COVER
P1-004_HUB
P1-005_STEEL_LEVER
P1-006_GRIP
P1-010_MAGNET_HOLDER
HW_MAGNET
P1-011A_HALL_FIXED_BRACKET
P1-011B_HALL_SENSOR_SLED
HW_HALL_PCB
HW_EXTENSION_SPRING_ENVELOPE
HW_STOP_PIN
HW_M6_STOP_SCREW_1
HW_M6_STOP_SCREW_2
HW_608_LEFT
HW_608_RIGHT
HW_INNER_RACE_SPACER
HW_AXIAL_SPACER_LEFT
HW_AXIAL_SPACER_RIGHT
HW_M8X90_PIVOT
HW_M8_BOLT_HEAD
HW_M8_NYLOC
HW_PRO_MICRO_ENVELOPE
P1-020_CLAMP_BASE_INTERFACE
P1-021_CLAMP_VERTICAL_BRACKET
P1-022_CLAMP_SCREW_GUIDE
P1-025_UPPER_RUBBER_PAD_HOLDER
HW_M10_CLAMP_SCREW
P1-024_SWIVEL_PAD_HOLDER
P1-023_CLAMP_KNOB
HW_M10_COUPLING_NUT
FIXTURE_DESK_10MM
