bvbvbv54/ELKATEB-Hydrolic-Handbrake/prototype_commercial_v1/step/P1C-P010_SPRING_COLLAR.step

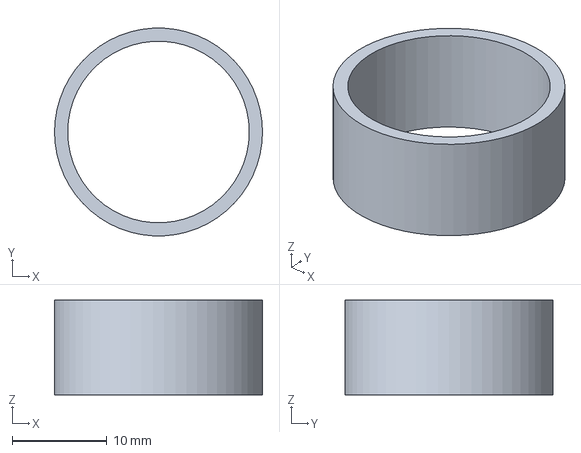
[picture p70: CAD file, 2026-09-27]
prototype_commercial_v1/step/P1C-P010_SPRING_COLLAR.step
22.0 x 22.0 x 10.0 mm
