bvbvbv54/ELKATEB-Hydrolic-Handbrake/prototype_commercial_v1/step/P1C-P009_SWIVEL_PAD.step

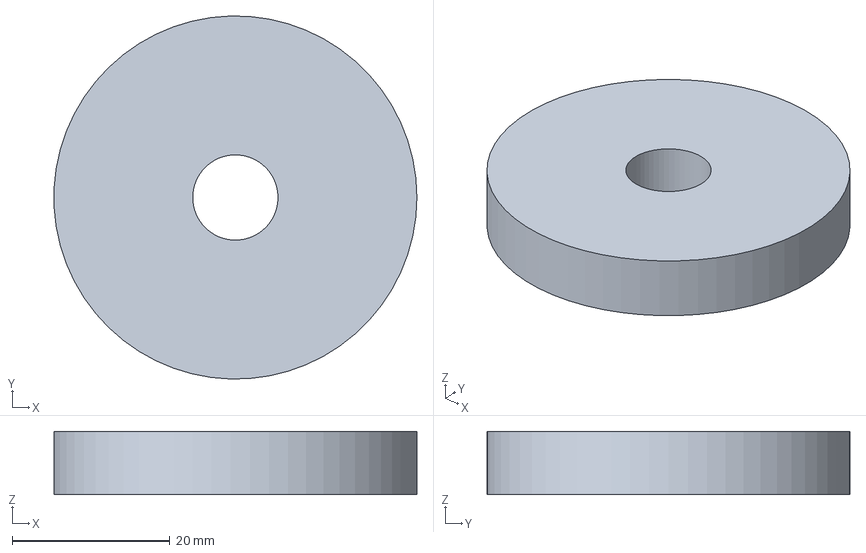
[picture p71: CAD file, 2026-09-27]
prototype_commercial_v1/step/P1C-P009_SWIVEL_PAD.step
46.0 x 46.0 x 8.00 mm
