bvbvbv54/ELKATEB-Hydrolic-Handbrake/prototype_commercial_v1/step/P1C-P006_ELECTRONICS_LID.step

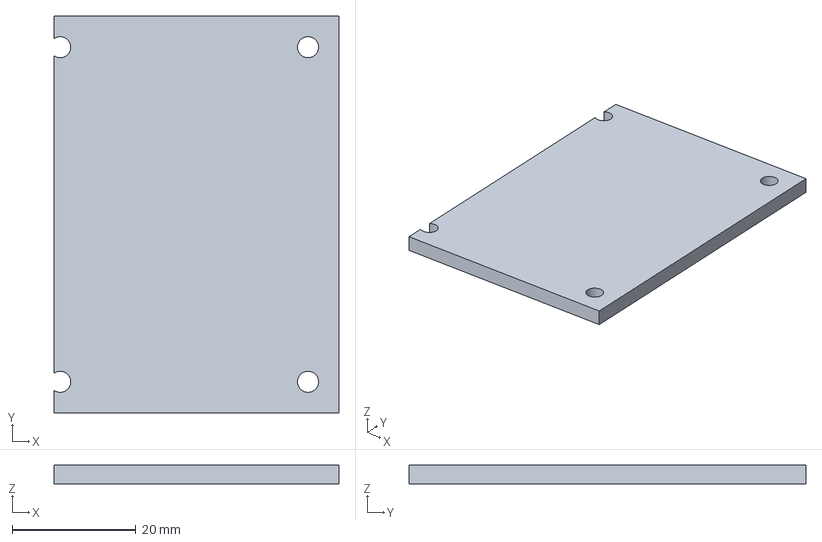
[picture p72: CAD file, 2026-09-27]
prototype_commercial_v1/step/P1C-P006_ELECTRONICS_LID.step
46.0 x 64.0 x 3.00 mm
