bvbvbv54/ELKATEB-Hydrolic-Handbrake/prototype_commercial_v1/step/P1C-S003_RIGHT_SIDE_FRAME.step

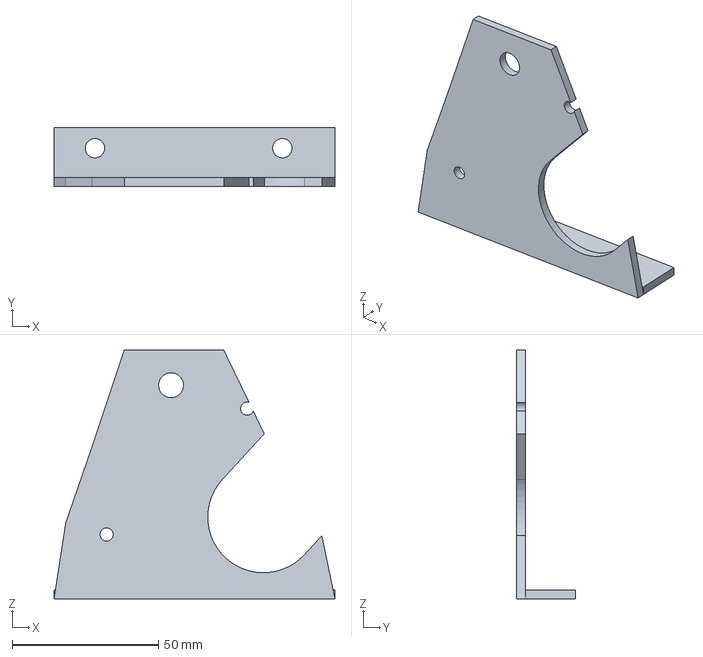
[picture p73: CAD file, 2026-09-27]
prototype_commercial_v1/step/P1C-S003_RIGHT_SIDE_FRAME.step
96.0 x 20.0 x 85.0 mm
