bvbvbv54/ELKATEB-Hydrolic-Handbrake/prototype_p1/step/P1-030_LEFT_BACKING_STRIP.step

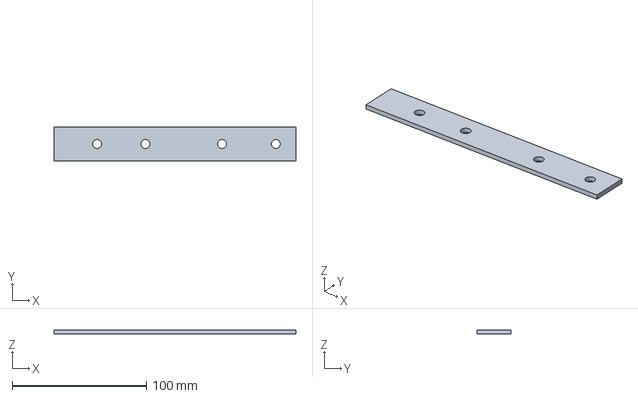
[picture p74: CAD file, 2026-09-27]
prototype_p1/step/P1-030_LEFT_BACKING_STRIP.step
180.0 x 25.0 x 3.00 mm
