bvbvbv54/ELKATEB-Hydrolic-Handbrake/prototype_commercial_v1/step/P1C-P003_HALL_WINDOW.step

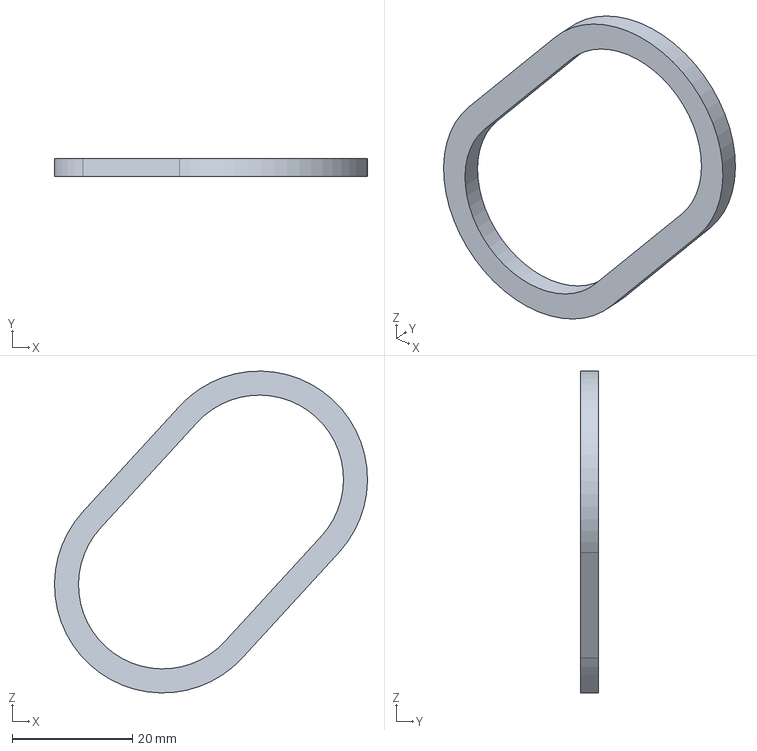
[picture p75: CAD file, 2026-09-27]
prototype_commercial_v1/step/P1C-P003_HALL_WINDOW.step
52.1 x 3.00 x 53.5 mm
