bvbvbv54/ELKATEB-Hydrolic-Handbrake/prototype_commercial_v1/step/P1C-P004_HALL_SLED.step

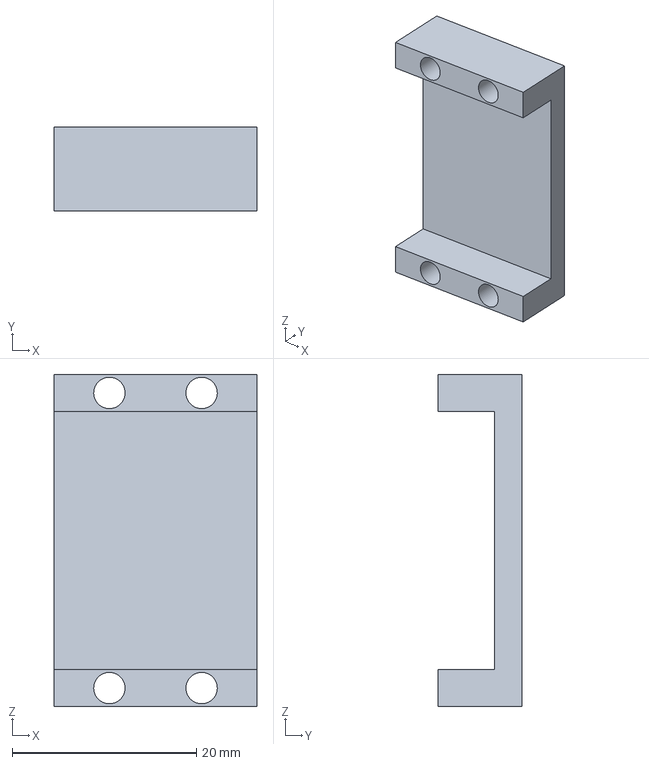
[picture p76: CAD file, 2026-09-27]
prototype_commercial_v1/step/P1C-P004_HALL_SLED.step
22.0 x 9.10 x 36.0 mm
