bvbvbv54/ELKATEB-Hydrolic-Handbrake/prototype_commercial_v1/step/P1C-S004_STEEL_LEVER.step

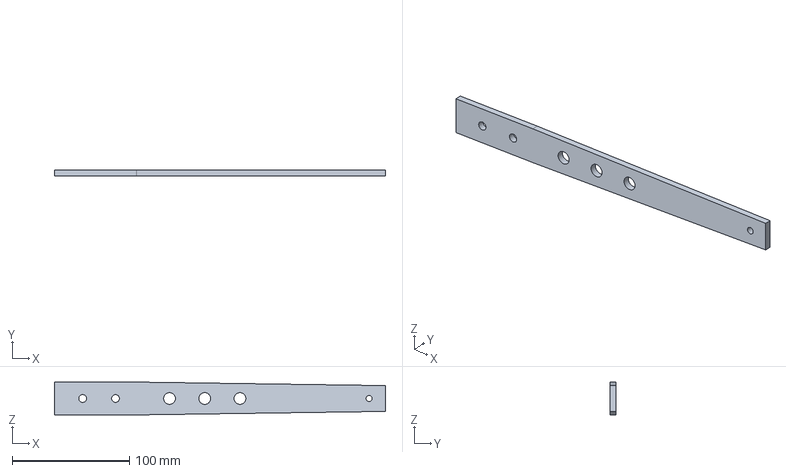
[picture p77: CAD file, 2026-09-27]
prototype_commercial_v1/step/P1C-S004_STEEL_LEVER.step
282.0 x 5.00 x 28.0 mm
