bvbvbv54/ELKATEB-Hydrolic-Handbrake/prototype_commercial_v1/step/P1C-P007_CABLE_GUIDE.step

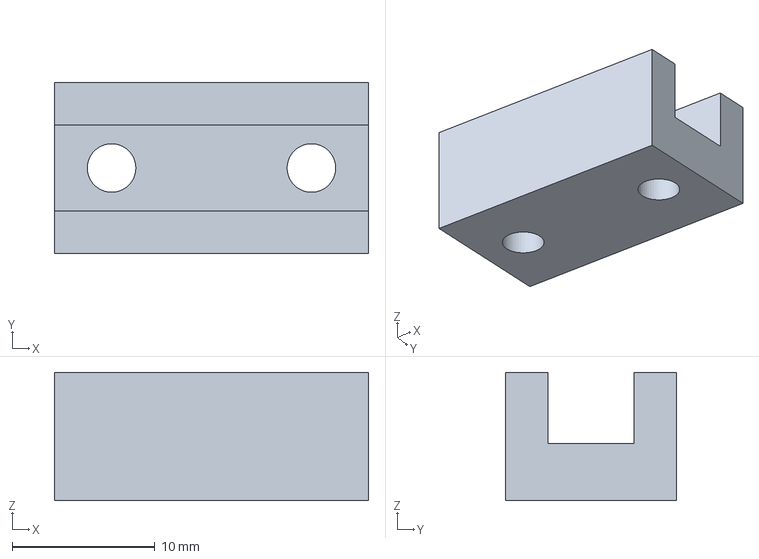
[picture p78: CAD file, 2026-09-27]
prototype_commercial_v1/step/P1C-P007_CABLE_GUIDE.step
22.0 x 12.0 x 9.00 mm
