bvbvbv54/ELKATEB-Hydrolic-Handbrake/prototype_commercial_v1/step/P1C_25_PERCENT.step

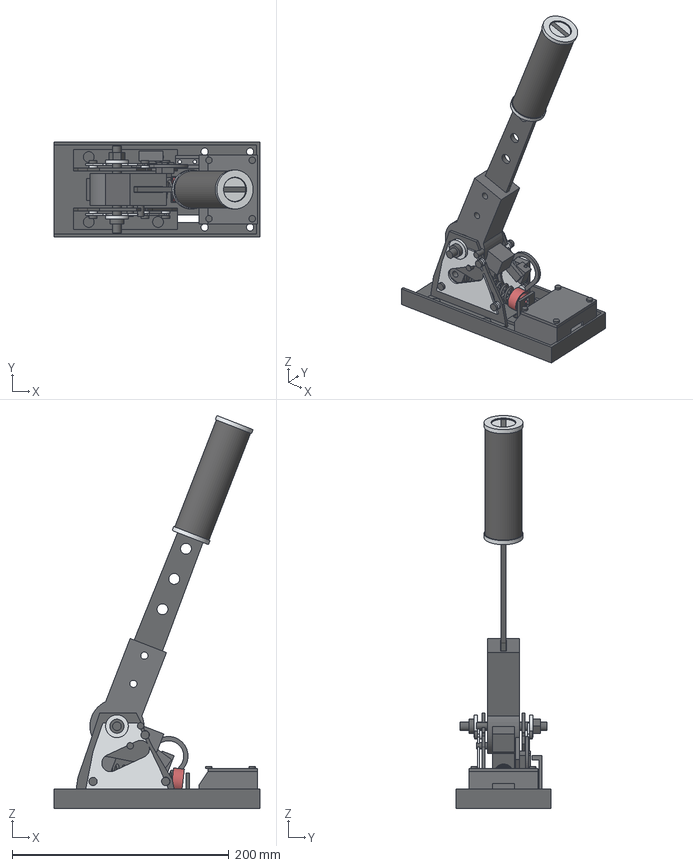
[picture p79: CAD file, 2026-09-27]
prototype_commercial_v1/step/P1C_25_PERCENT.step
190.0 x 88.0 x 363.1 mm
P1C-S001_BASE_TRAY
P1C-S002_LEFT_SIDE_FRAME
P1C-S003_RIGHT_SIDE_FRAME
P1C-S005_SPRING_BRACKET
P1C-A001_LEFT_ACCENT
P1C-A002_RIGHT_ACCENT
P1C-P001_BEARING_HUB
P1C-S004_STEEL_LEVER
HW_GRIP_CORE
HW_RUBBER_GRIP
HW_GRIP_TRIM_RING_1
HW_GRIP_TRIM_RING_2
HW_EXTENSION_SPRING
P1C-P010_SPRING_COLLAR
HW_STOP_PIN
HW_M6_STOP_1
HW_M6_STOP_2
P1C-P002_MAGNET_CARRIER
HW_MAGNET
P1C-P003_HALL_WINDOW
P1C-P004_HALL_SLED
HW_HALL_PCB
P1C-P005_ELECTRONICS_POD
P1C-P006_ELECTRONICS_LID
P1C-P007_CABLE_GUIDE
HW_608_LEFT
HW_608_RIGHT
HW_M8_PIVOT
HW_PIVOT_WASHER_LEFT
HW_PIVOT_WASHER_RIGHT
HW_M8_BOLT_HEAD
HW_M8_NYLOC
HW_LEFT_M4_36
HW_LEFT_HEAD_36
HW_RIGHT_M4_36
HW_RIGHT_HEAD_36
HW_LEFT_M4_84
HW_LEFT_HEAD_84
HW_RIGHT_M4_84
HW_RIGHT_HEAD_84
HW_LEFT_M4_103
HW_LEFT_HEAD_103
HW_RIGHT_M4_103
HW_RIGHT_HEAD_103
HW_M6_FRAME_32_14
HW_M6_FRAME_96_14
HW_M6_FRAME_32_74
HW_M6_FRAME_96_74
HW_M3_LID_143_17
HW_M3_LID_183_17
HW_M3_LID_143_71
HW_M3_LID_183_71
