bvbvbv54/ELKATEB-Hydrolic-Handbrake/prototype_commercial_v1/step/P1C-S001_BASE_TRAY.step

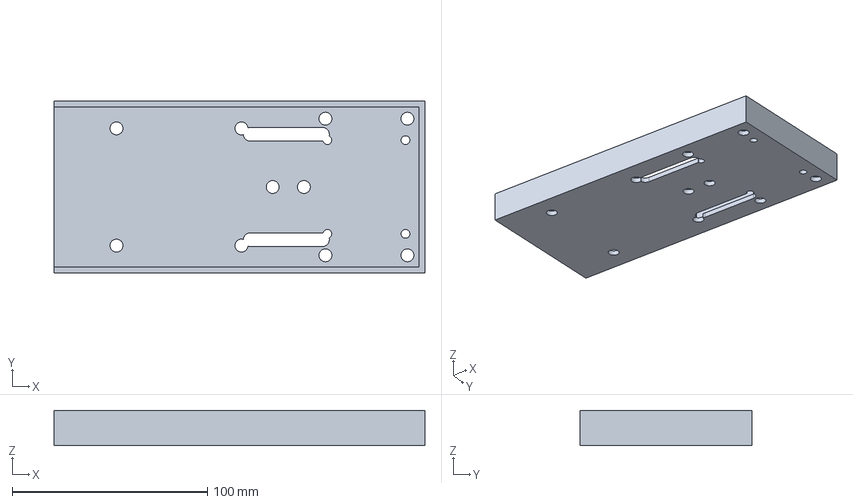
[picture p80: CAD file, 2026-09-27]
prototype_commercial_v1/step/P1C-S001_BASE_TRAY.step
190.0 x 88.0 x 18.0 mm
