bvbvbv54/ELKATEB-Hydrolic-Handbrake/prototype_commercial_v1/step/P1C-S005_SPRING_BRACKET.step

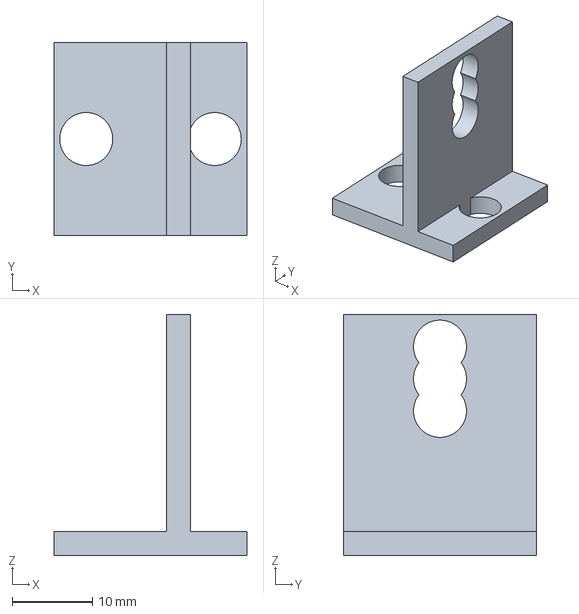
[picture p85: CAD file, 2026-09-27]
prototype_commercial_v1/step/P1C-S005_SPRING_BRACKET.step
24.0 x 24.0 x 30.0 mm
