bvbvbv54/ELKATEB-Hydrolic-Handbrake/prototype_commercial_v1/renders/10_ACCENT_PANEL_INSTALLATION.png

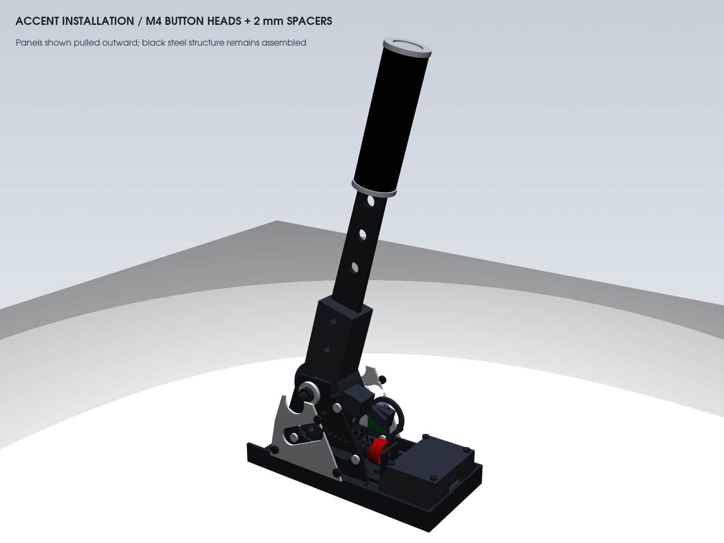
prototype_commercial_v1/renders/10_ACCENT_PANEL_INSTALLATION.png
